LuCy4n3/SmartPotProject/Programmer/iot-sunxi-driver/Documentation/images/DotNetIotRoadmapComponents.png

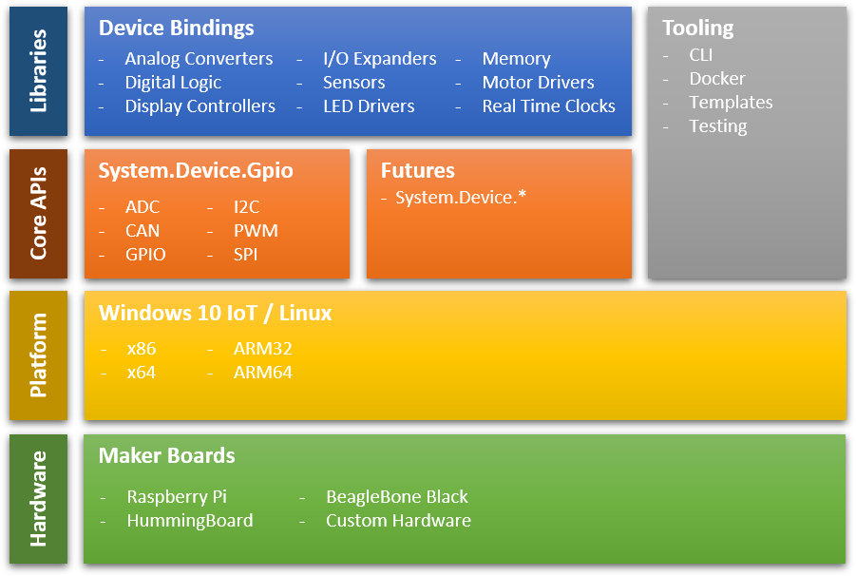
Programmer/iot-sunxi-driver/Documentation/images/DotNetIotRoadmapComponents.png
