LuCy4n3/SmartPotProject/Programmer/Bottom - lumina normala.png

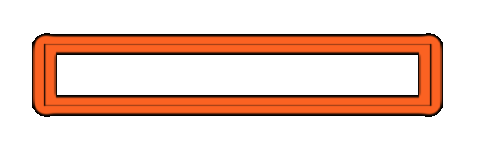
Programmer/Bottom - lumina normala.png
