LuCy4n3/SmartPotProject/Programmer/iot-sunxi-driver/Documentation/images/configurations.png

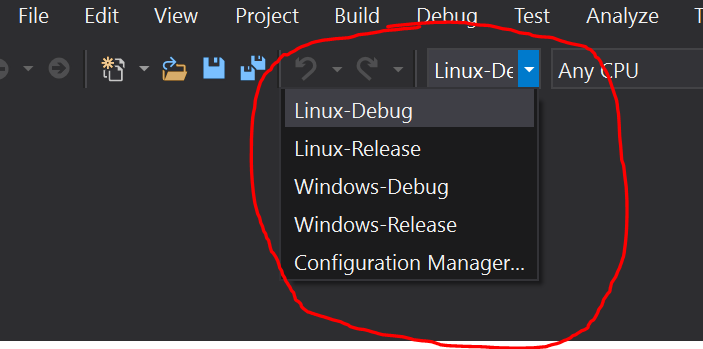
Programmer/iot-sunxi-driver/Documentation/images/configurations.png
