LuCy4n3/SmartPotProject/Programmer/iot-sunxi-driver/samples/force-sensitive-resistor/Fsr408_Capacitor_RaspPi.png

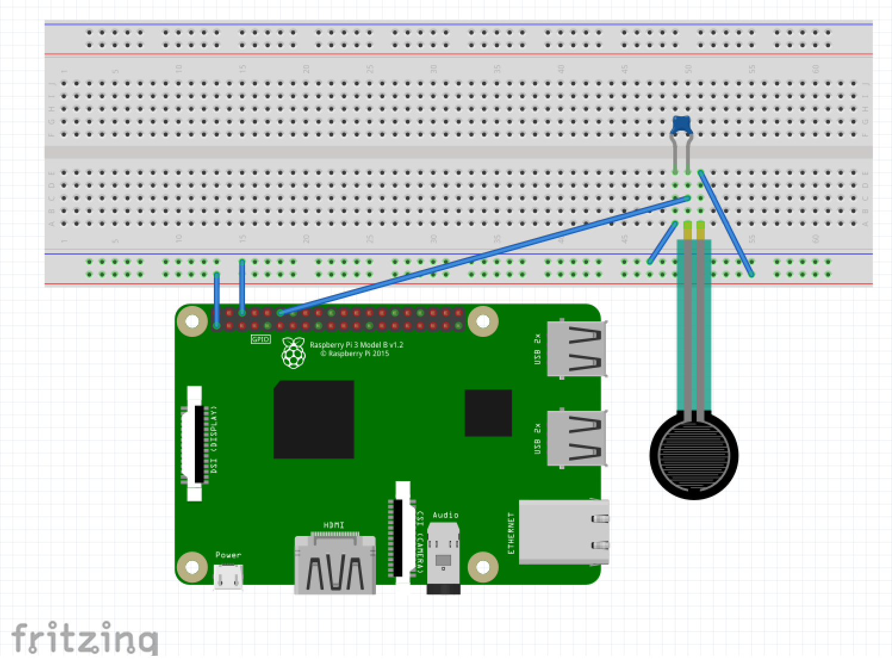
Programmer/iot-sunxi-driver/samples/force-sensitive-resistor/Fsr408_Capacitor_RaspPi.png
