LuCy4n3/SmartPotProject/Programmer/iot-sunxi-driver/samples/force-sensitive-resistor/Fsr408_Mcp3008_RaspPi.png

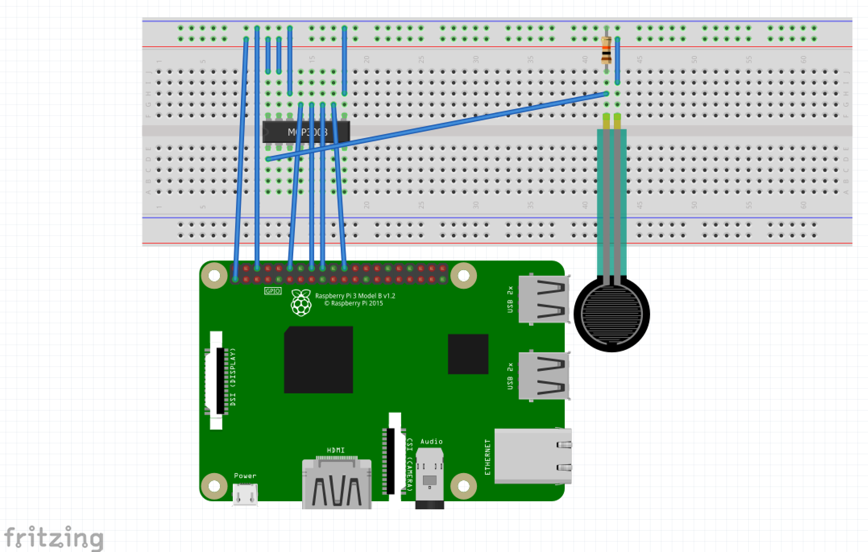
Programmer/iot-sunxi-driver/samples/force-sensitive-resistor/Fsr408_Mcp3008_RaspPi.png
