LuCy4n3/SmartPotProject/Programmer/iot-sunxi-driver/samples/led-blink/rpi-led_bb.png

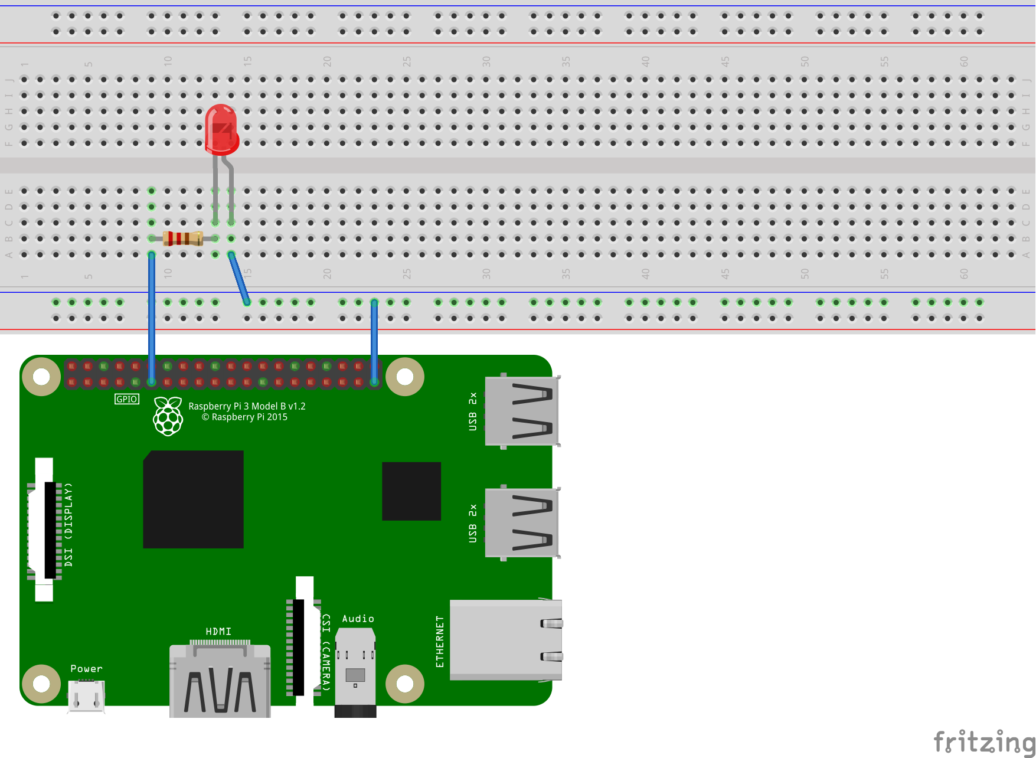
Programmer/iot-sunxi-driver/samples/led-blink/rpi-led_bb.png
