LuCy4n3/SmartPotProject/Programmer/iot-sunxi-driver/samples/led-matrix-weather/chaining-matrices.jpg

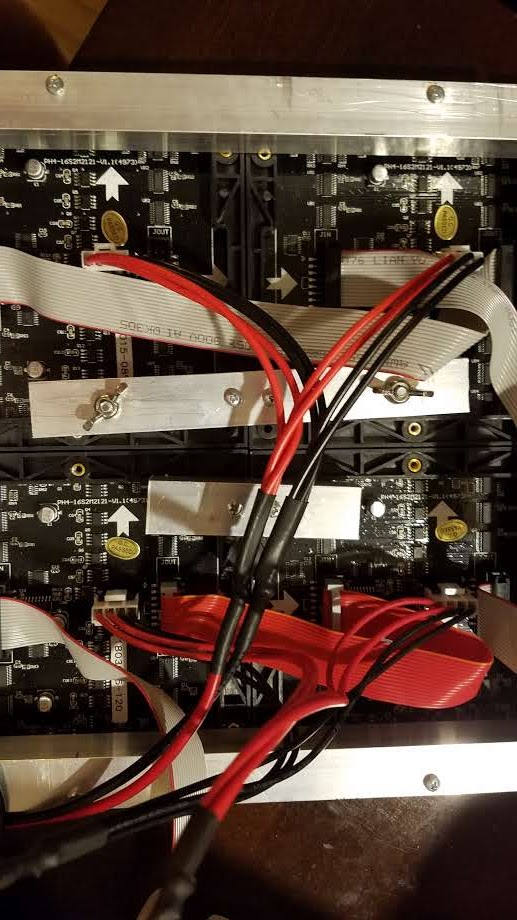
Programmer/iot-sunxi-driver/samples/led-matrix-weather/chaining-matrices.jpg
