LuCy4n3/SmartPotProject/Programmer/iot-sunxi-driver/samples/led-matrix-weather/pi-with-bonnet.jpg

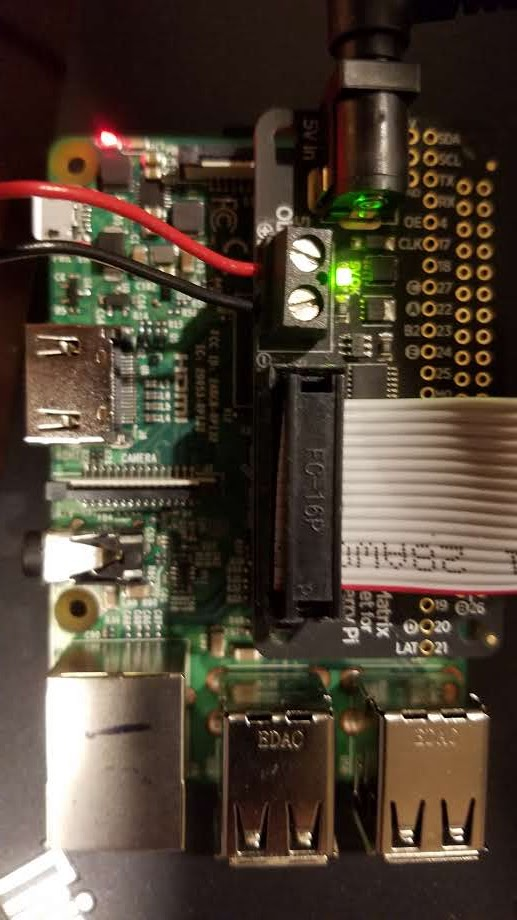
Programmer/iot-sunxi-driver/samples/led-matrix-weather/pi-with-bonnet.jpg
