LuCy4n3/SmartPotProject/Programmer/iot-sunxi-driver/samples/led-matrix-weather/rain.jpg

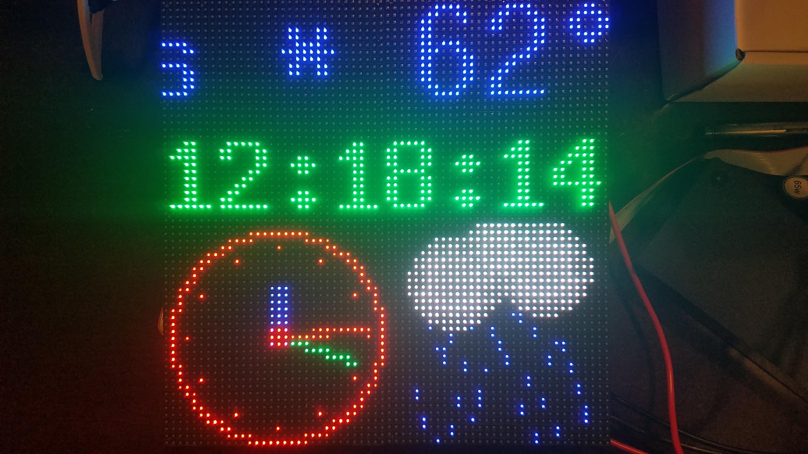
Programmer/iot-sunxi-driver/samples/led-matrix-weather/rain.jpg
