LuCy4n3/SmartPotProject/Programmer/iot-sunxi-driver/samples/led-more-blinking-lights/rpi-more-blinking-lights_bb.png

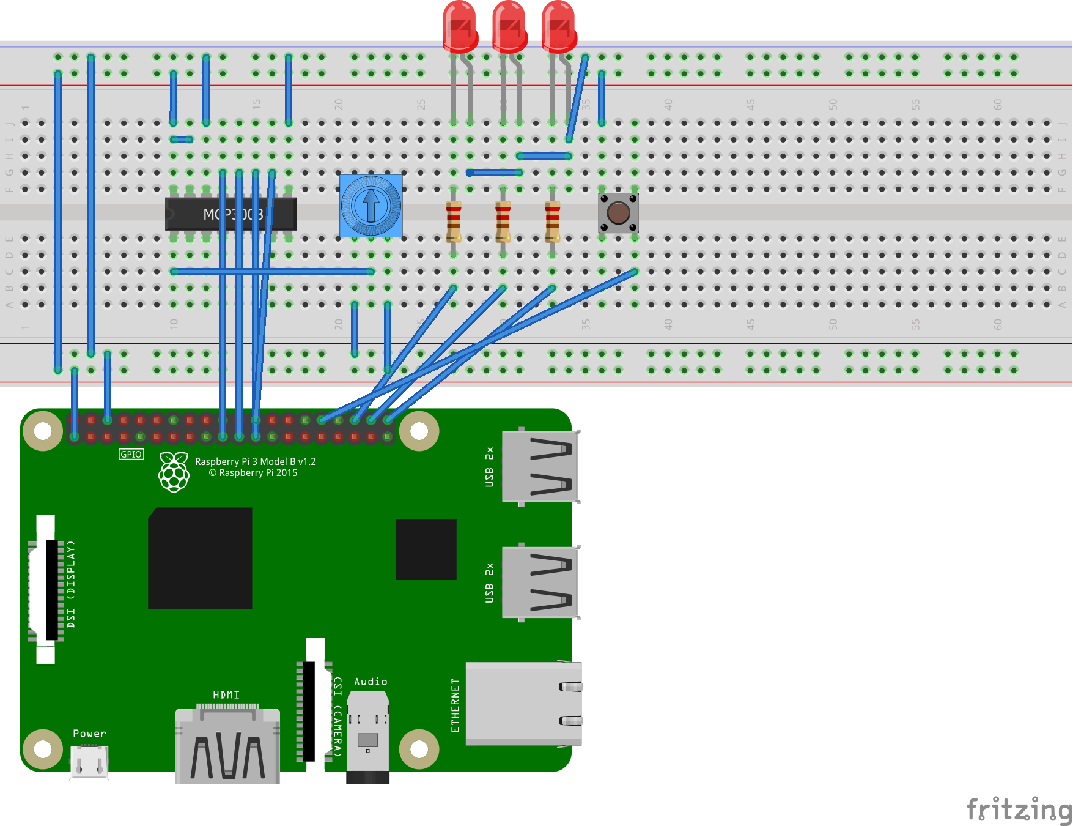
Programmer/iot-sunxi-driver/samples/led-more-blinking-lights/rpi-more-blinking-lights_bb.png
