LuCy4n3/SmartPotProject/Programmer/iot-sunxi-driver/samples/serialport-arduino/arduino-pi-sp_bb.png

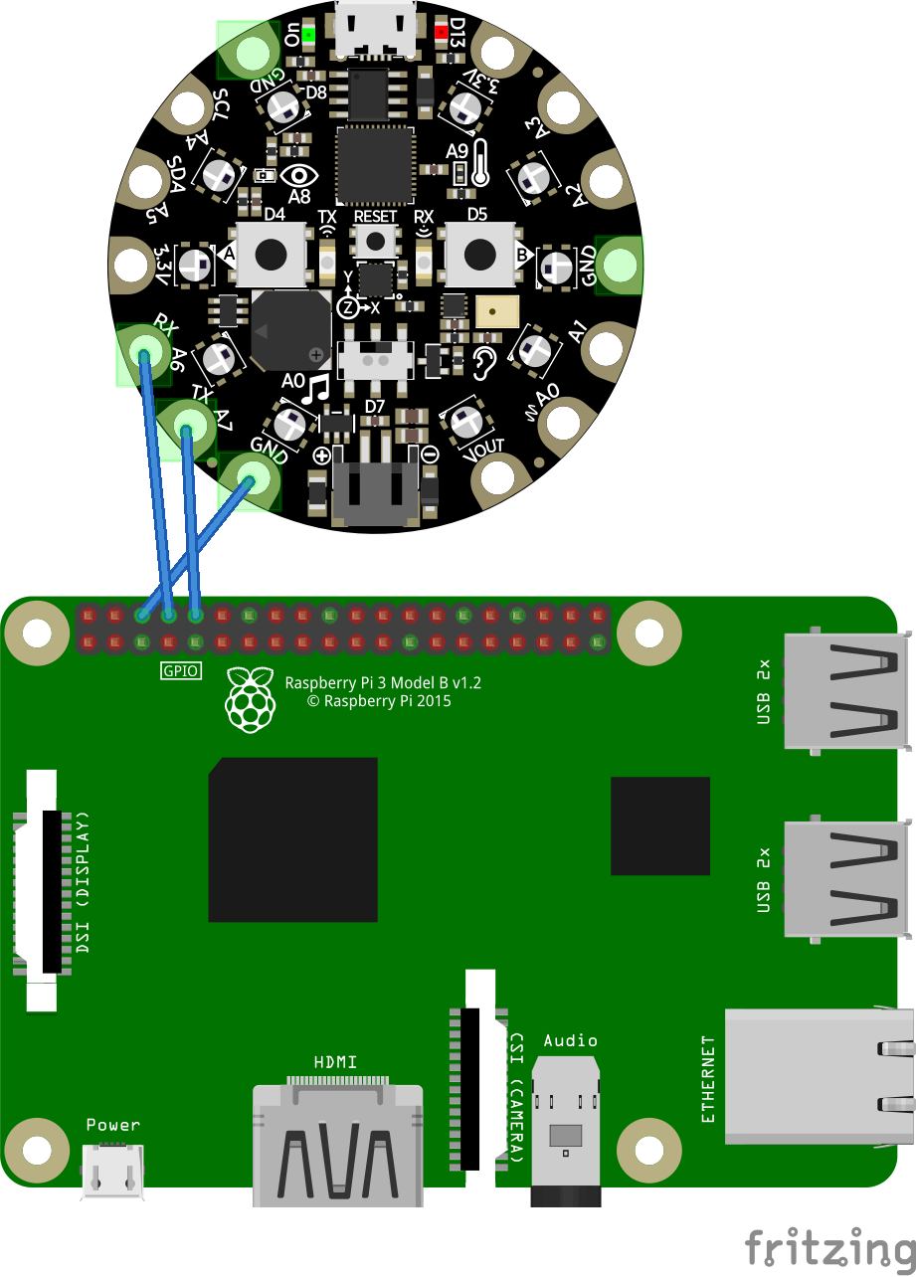
Programmer/iot-sunxi-driver/samples/serialport-arduino/arduino-pi-sp_bb.png
