LuCy4n3/SmartPotProject/Programmer/iot-sunxi-driver/src/devices/Ads1115/samples/ADS1115_circuit_bb.png

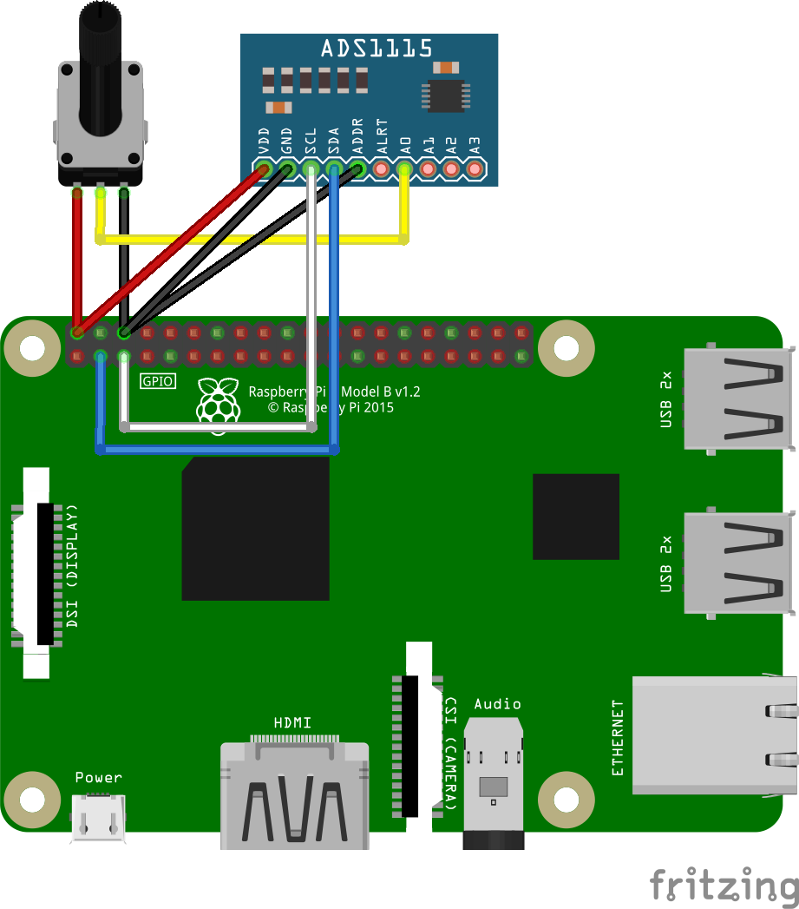
Programmer/iot-sunxi-driver/src/devices/Ads1115/samples/ADS1115_circuit_bb.png
