LuCy4n3/SmartPotProject/Programmer/iot-sunxi-driver/src/devices/Ads1115/sensor.jpg

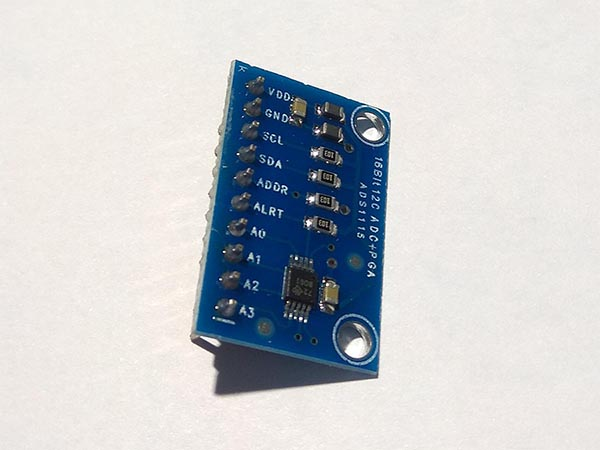
Programmer/iot-sunxi-driver/src/devices/Ads1115/sensor.jpg
