LuCy4n3/SmartPotProject/Programmer/iot-sunxi-driver/src/devices/Adxl345/samples/ADXL345_circuit_bb.png

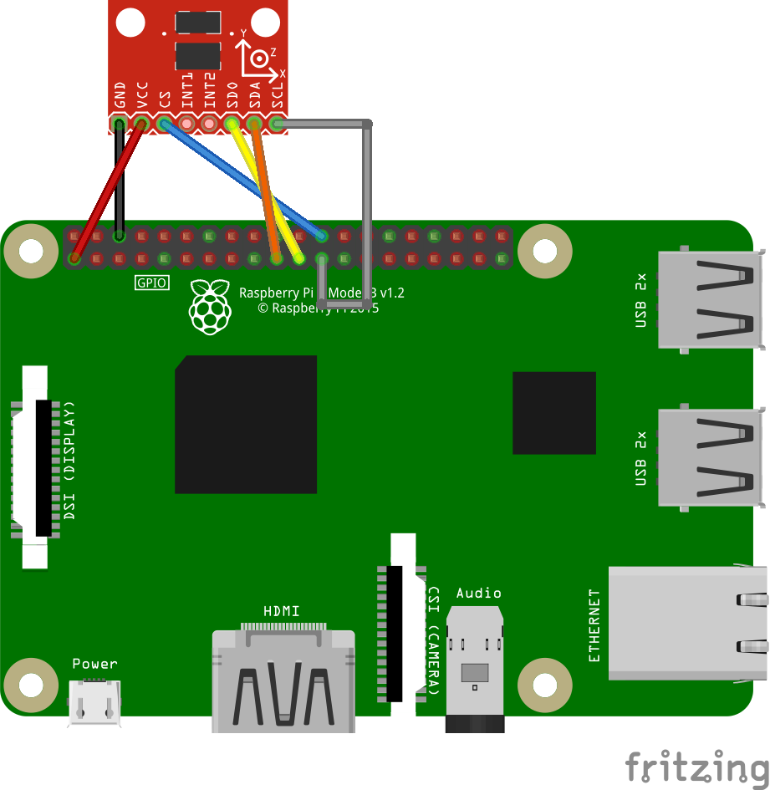
Programmer/iot-sunxi-driver/src/devices/Adxl345/samples/ADXL345_circuit_bb.png
