LuCy4n3/SmartPotProject/Programmer/iot-sunxi-driver/src/devices/Adxl345/sensor.jpg

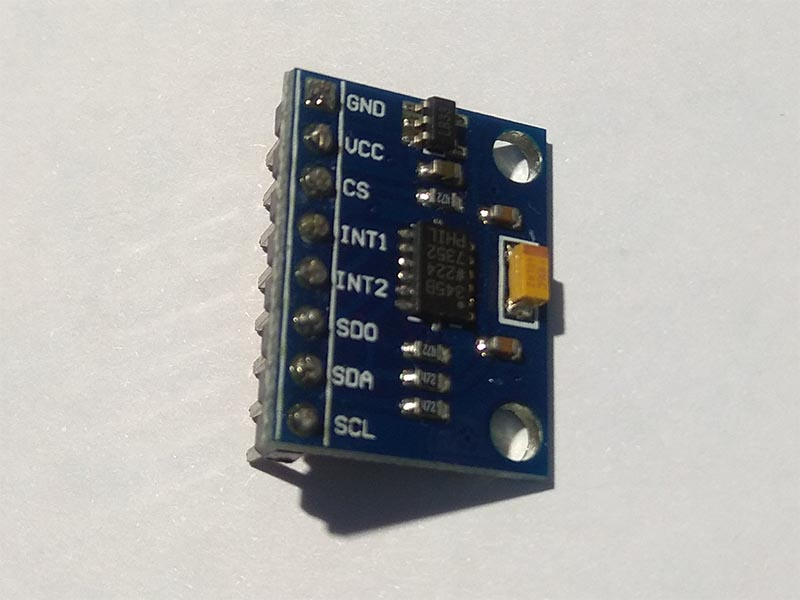
Programmer/iot-sunxi-driver/src/devices/Adxl345/sensor.jpg
