LuCy4n3/SmartPotProject/Programmer/iot-sunxi-driver/src/devices/Ags01db/samples/AGS01DB_circuit_bb.png

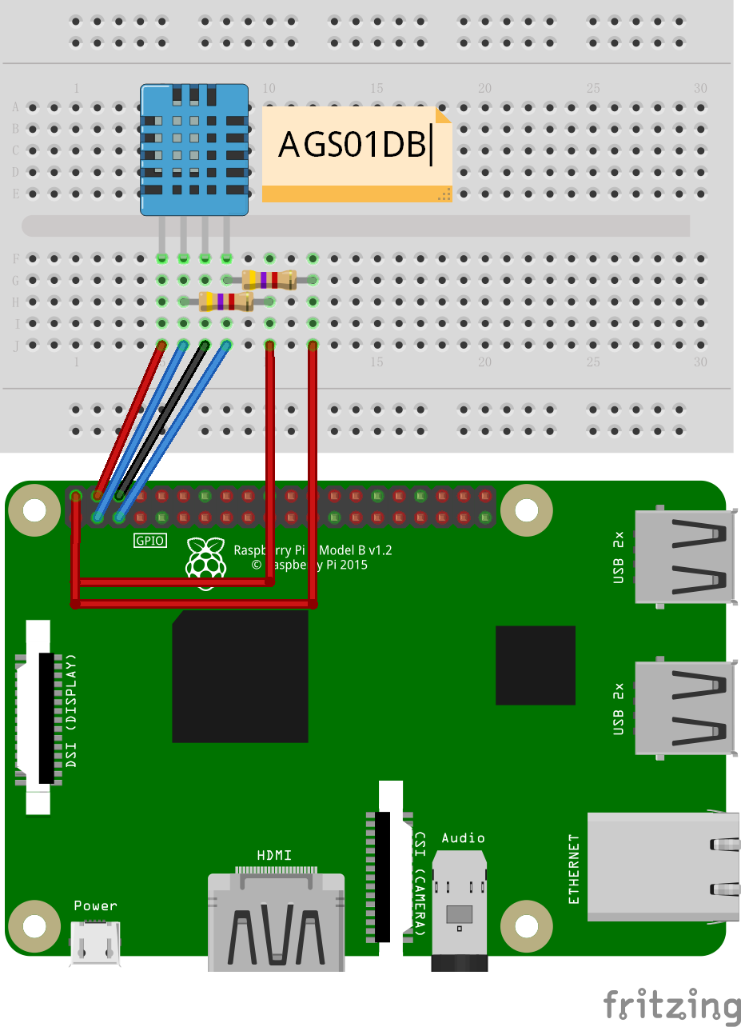
Programmer/iot-sunxi-driver/src/devices/Ags01db/samples/AGS01DB_circuit_bb.png
