LuCy4n3/SmartPotProject/Programmer/iot-sunxi-driver/src/devices/Ags01db/sensor.jpg

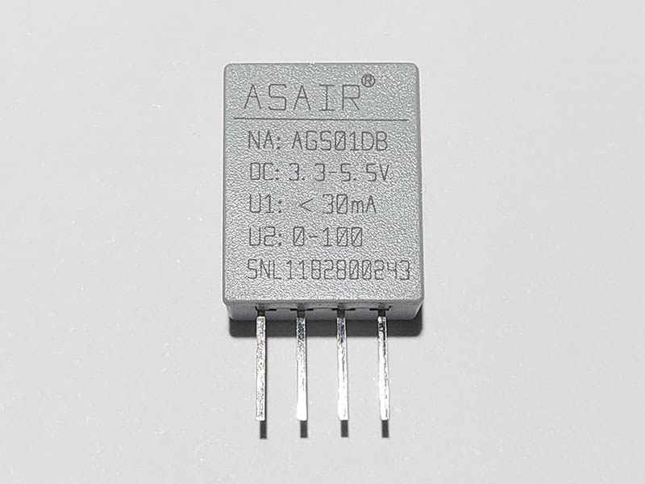
Programmer/iot-sunxi-driver/src/devices/Ags01db/sensor.jpg
