LuCy4n3/SmartPotProject/Programmer/iot-sunxi-driver/src/devices/Ak8963/corrcalib.png

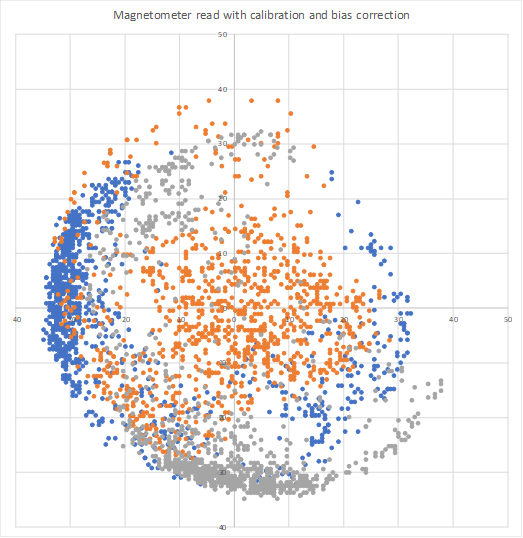
Programmer/iot-sunxi-driver/src/devices/Ak8963/corrcalib.png
