LuCy4n3/SmartPotProject/Programmer/iot-sunxi-driver/src/devices/Ak8963/rawcalib.png

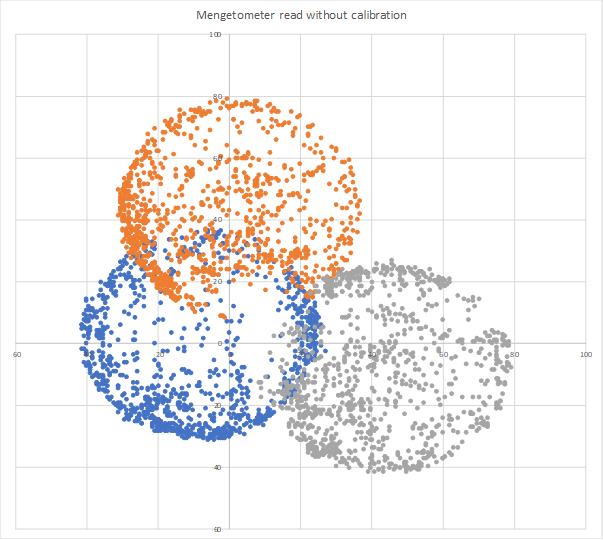
Programmer/iot-sunxi-driver/src/devices/Ak8963/rawcalib.png
