LuCy4n3/SmartPotProject/Programmer/iot-sunxi-driver/src/devices/Bh1745/sensor.jpg

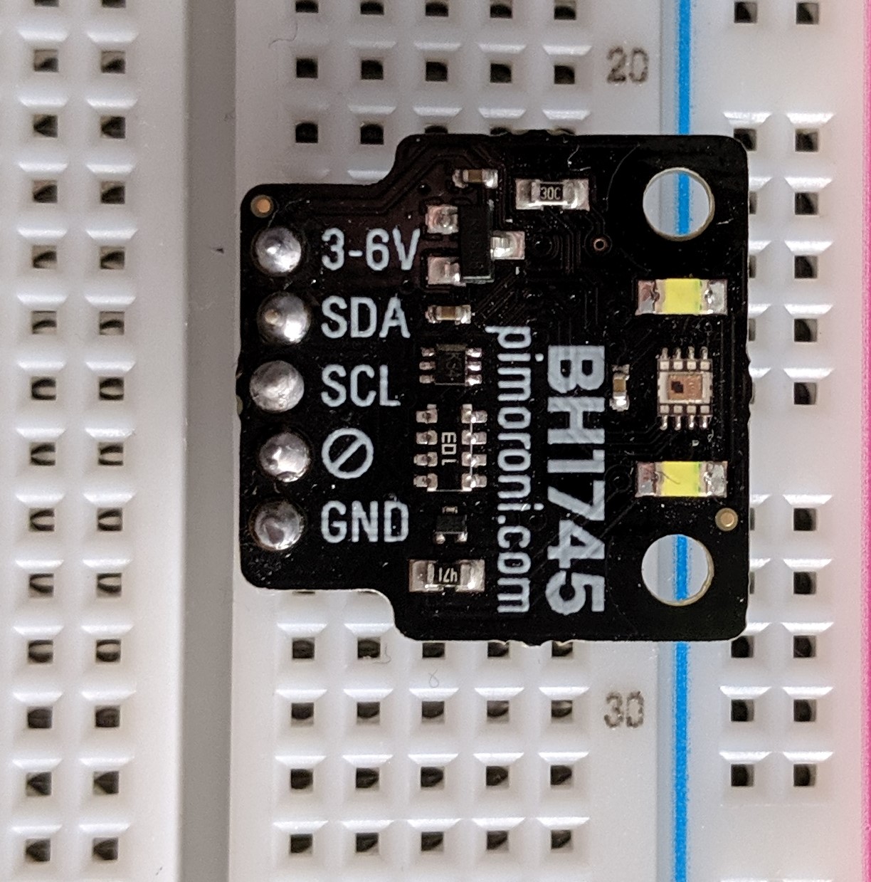
Programmer/iot-sunxi-driver/src/devices/Bh1745/sensor.jpg
