LuCy4n3/SmartPotProject/Programmer/iot-sunxi-driver/src/devices/Bh1750fvi/samples/BH1750FVI_Circuit_bb.png

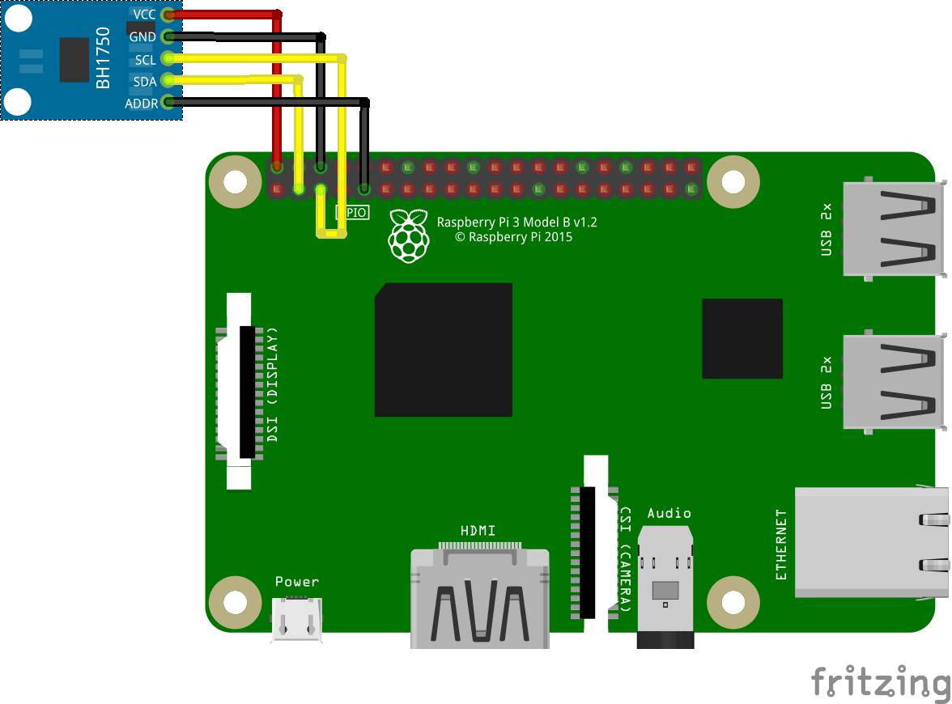
Programmer/iot-sunxi-driver/src/devices/Bh1750fvi/samples/BH1750FVI_Circuit_bb.png
