LuCy4n3/SmartPotProject/Programmer/iot-sunxi-driver/src/devices/Bh1750fvi/sensor.jpg

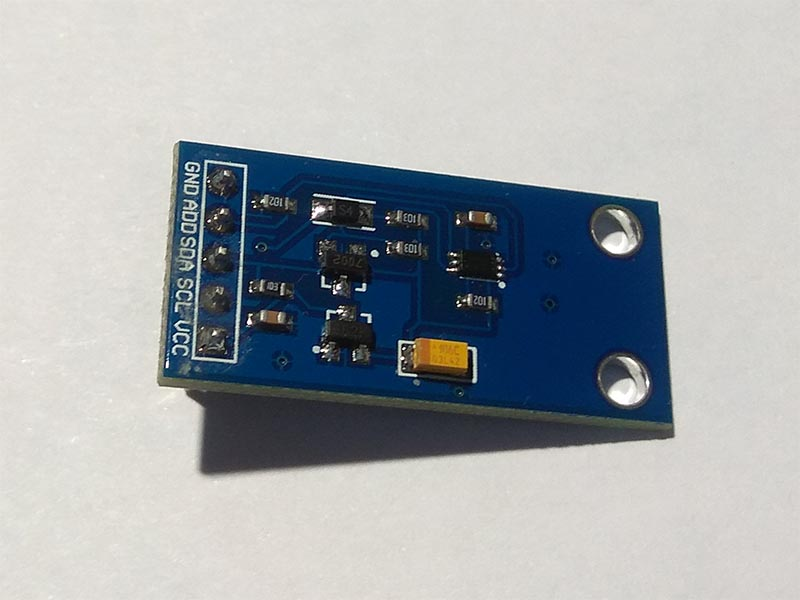
Programmer/iot-sunxi-driver/src/devices/Bh1750fvi/sensor.jpg
