LuCy4n3/SmartPotProject/Programmer/iot-sunxi-driver/src/devices/Bmp180/samples/rpi-bmp180_i2c_bb.png

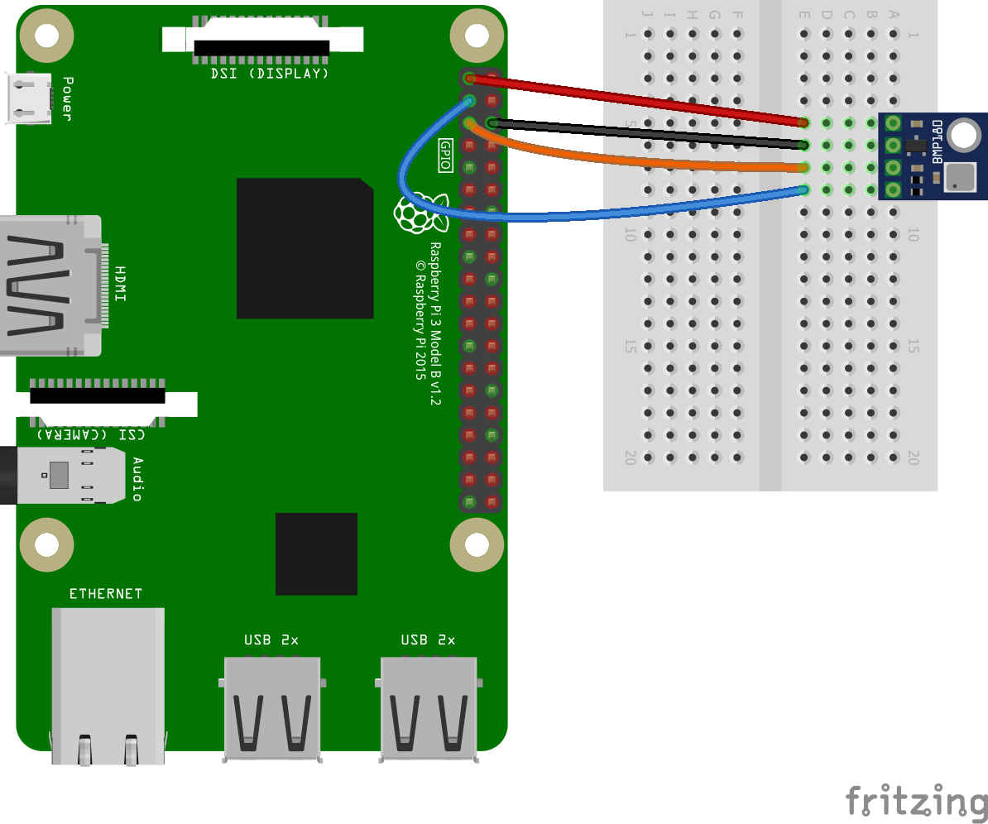
Programmer/iot-sunxi-driver/src/devices/Bmp180/samples/rpi-bmp180_i2c_bb.png
