LuCy4n3/SmartPotProject/Programmer/iot-sunxi-driver/src/devices/Bmxx80/samples/rpi-bmp280_i2c.png

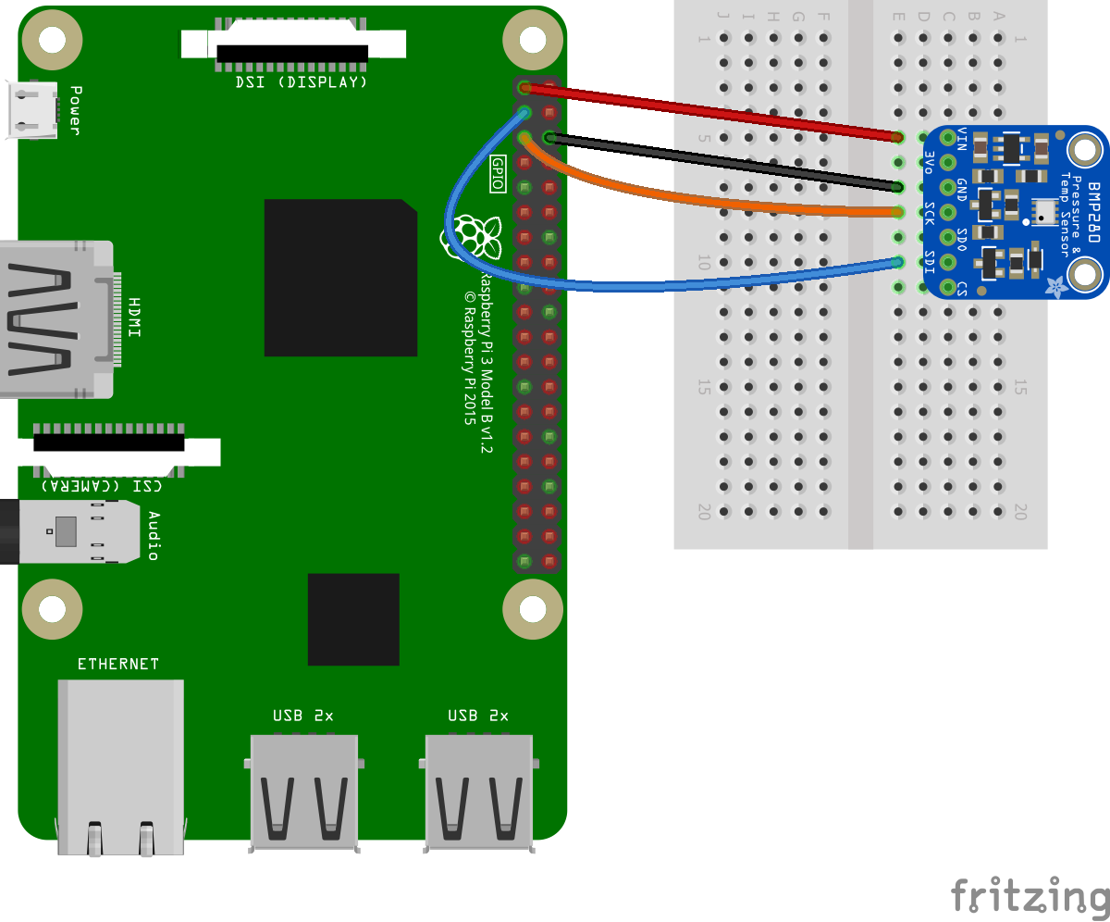
Programmer/iot-sunxi-driver/src/devices/Bmxx80/samples/rpi-bmp280_i2c.png
