LuCy4n3/SmartPotProject/Programmer/iot-sunxi-driver/src/devices/Bno055/BNO055.jpg

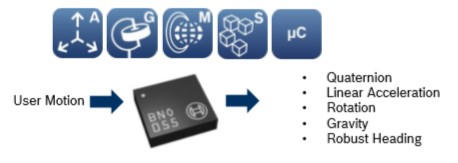
Programmer/iot-sunxi-driver/src/devices/Bno055/BNO055.jpg
