LuCy4n3/SmartPotProject/Programmer/iot-sunxi-driver/src/devices/BrickPi3/BrickPi3-How-it-Works.jpg

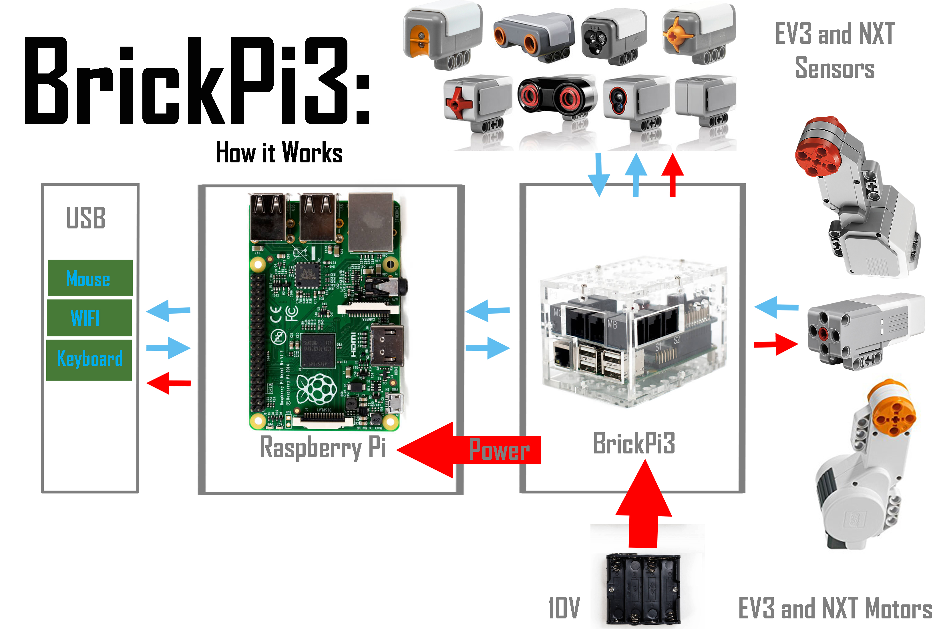
Programmer/iot-sunxi-driver/src/devices/BrickPi3/BrickPi3-How-it-Works.jpg
