LuCy4n3/SmartPotProject/Programmer/iot-sunxi-driver/src/devices/DCMotor/samples/dcmotor_bb.png

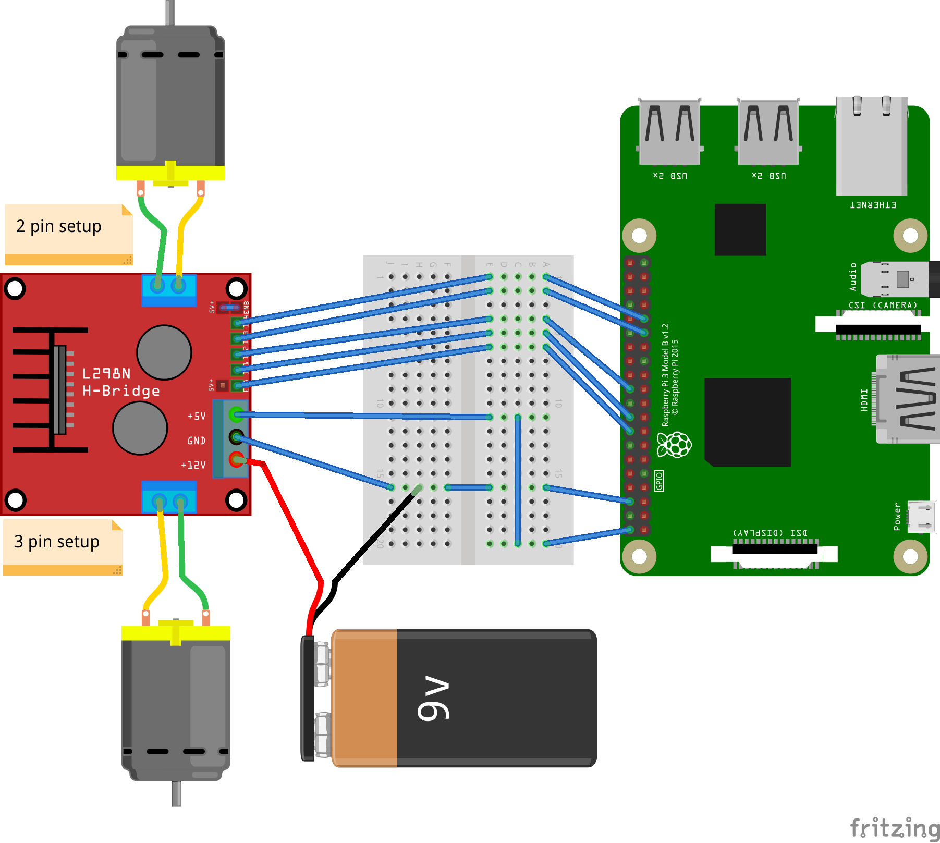
Programmer/iot-sunxi-driver/src/devices/DCMotor/samples/dcmotor_bb.png
