LuCy4n3/SmartPotProject/Programmer/iot-sunxi-driver/src/devices/Dhtxx/imgs/dht11.jpg

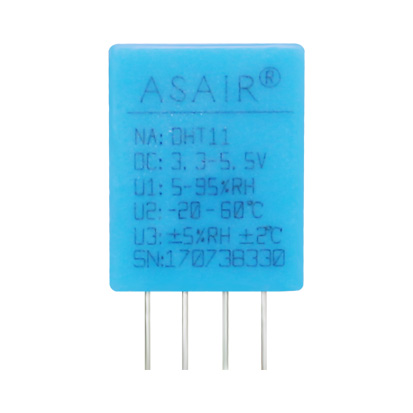
Programmer/iot-sunxi-driver/src/devices/Dhtxx/imgs/dht11.jpg
