LuCy4n3/SmartPotProject/Programmer/iot-sunxi-driver/src/devices/Dhtxx/samples/dht22.png

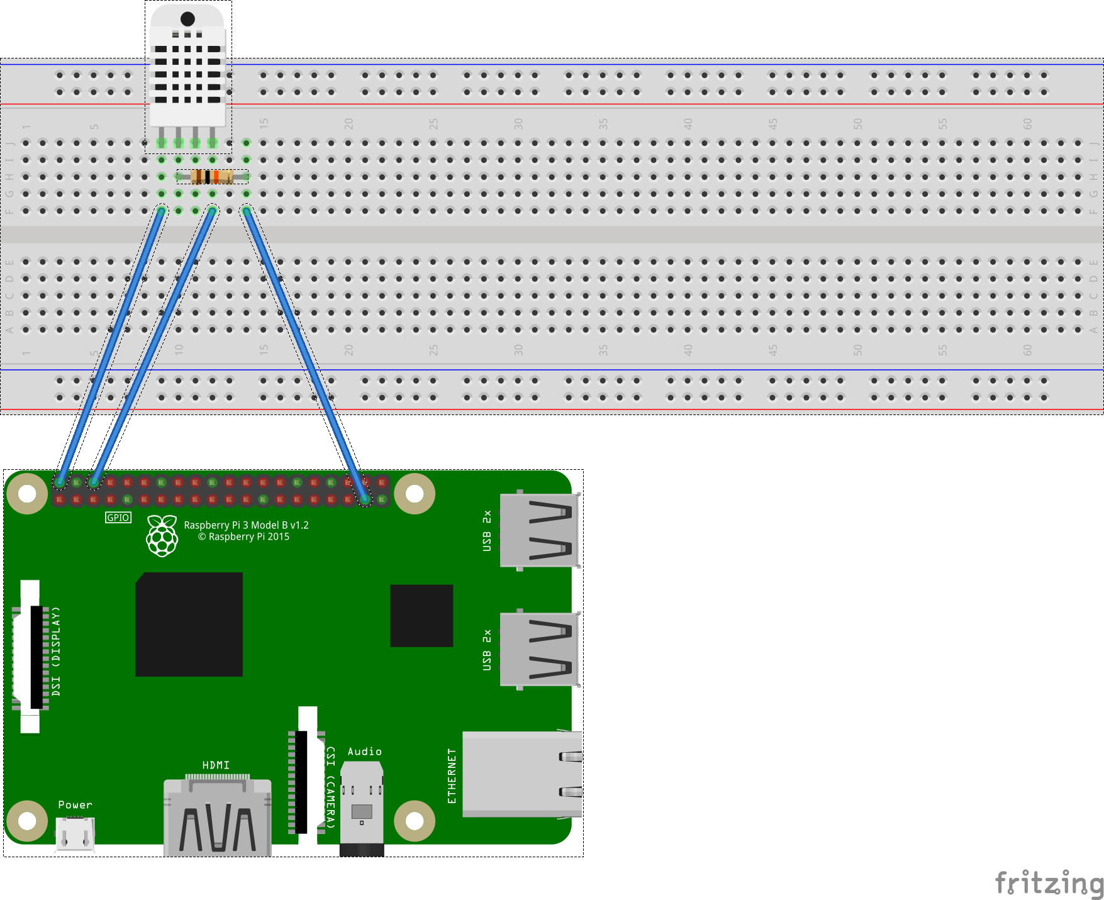
Programmer/iot-sunxi-driver/src/devices/Dhtxx/samples/dht22.png
