LuCy4n3/SmartPotProject/Programmer/iot-sunxi-driver/src/devices/Dhtxx/samples/dht22ex.jpg

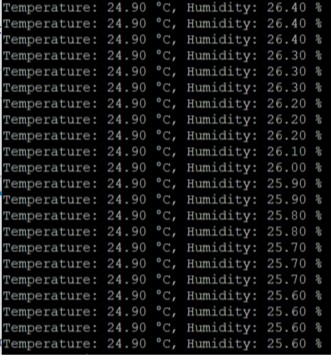
Programmer/iot-sunxi-driver/src/devices/Dhtxx/samples/dht22ex.jpg
