LuCy4n3/SmartPotProject/Programmer/iot-sunxi-driver/src/devices/GoPiGo3/GoPiGo3.png

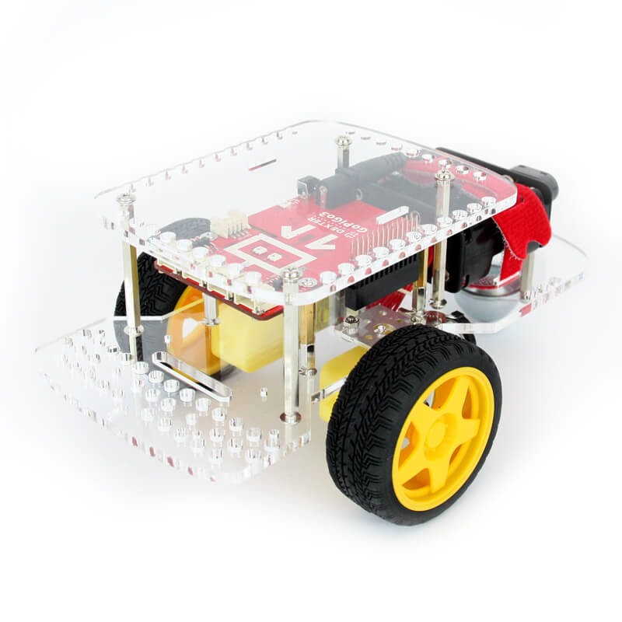
Programmer/iot-sunxi-driver/src/devices/GoPiGo3/GoPiGo3.png
