LuCy4n3/SmartPotProject/Programmer/iot-sunxi-driver/src/devices/GoPiGo3/gopigosensors.png

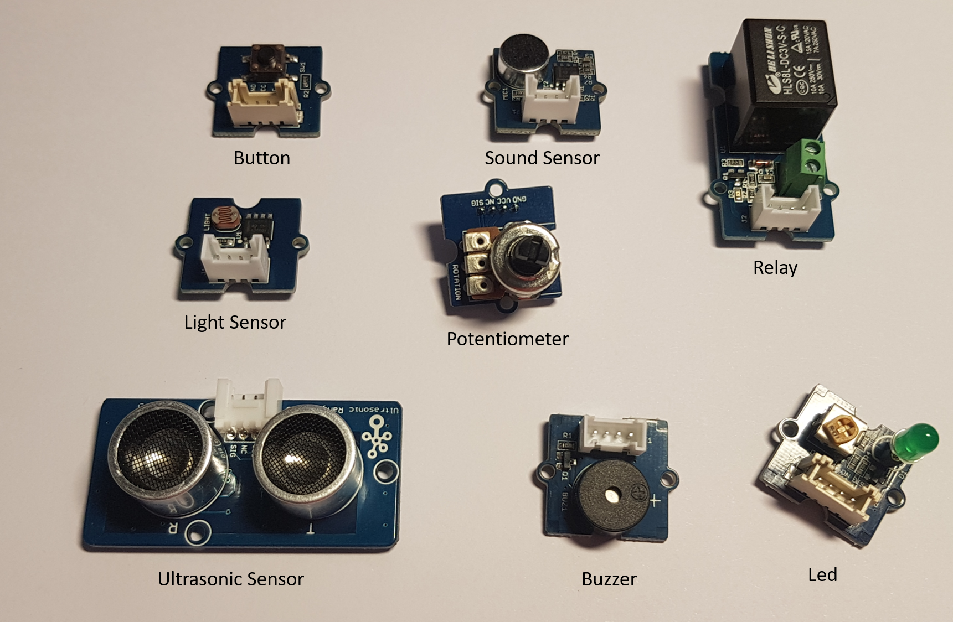
Programmer/iot-sunxi-driver/src/devices/GoPiGo3/gopigosensors.png
