LuCy4n3/SmartPotProject/Programmer/iot-sunxi-driver/src/devices/GrovePi/grovepi.jpg

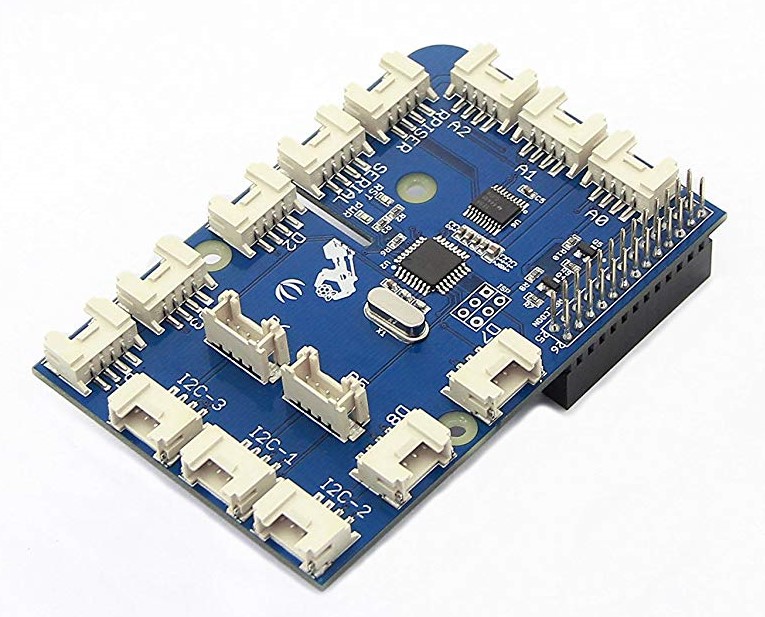
Programmer/iot-sunxi-driver/src/devices/GrovePi/grovepi.jpg
