LuCy4n3/SmartPotProject/Programmer/iot-sunxi-driver/src/devices/GrovePi/GrovePort.png

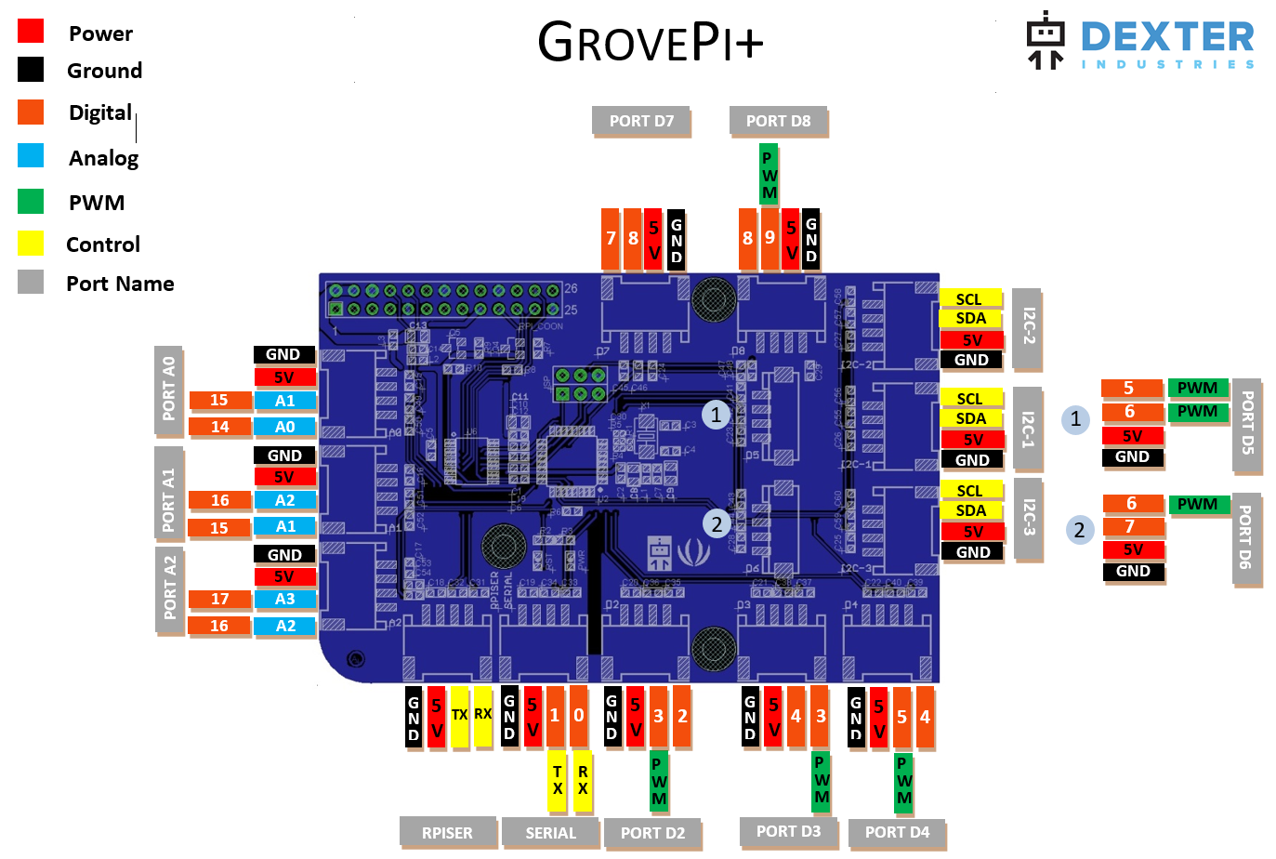
Programmer/iot-sunxi-driver/src/devices/GrovePi/GrovePort.png
