LuCy4n3/SmartPotProject/Programmer/iot-sunxi-driver/src/devices/GrovePi/samples/sample.jpg

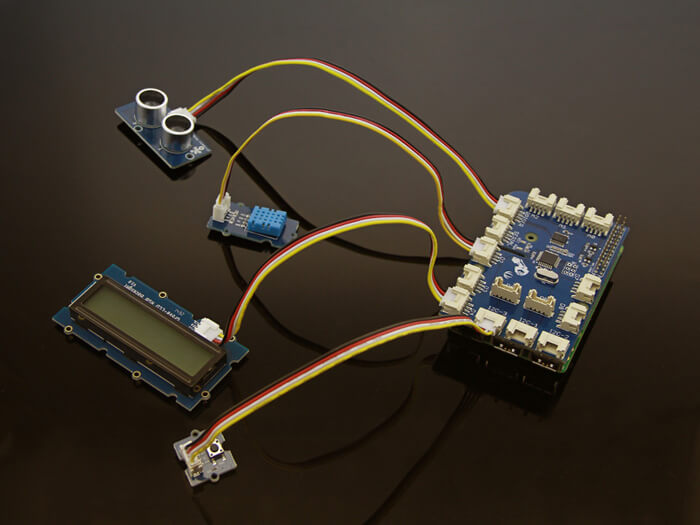
Programmer/iot-sunxi-driver/src/devices/GrovePi/samples/sample.jpg
