LuCy4n3/SmartPotProject/Programmer/iot-sunxi-driver/src/devices/Hcsr04/samples/raspberry_hc-sr04.png

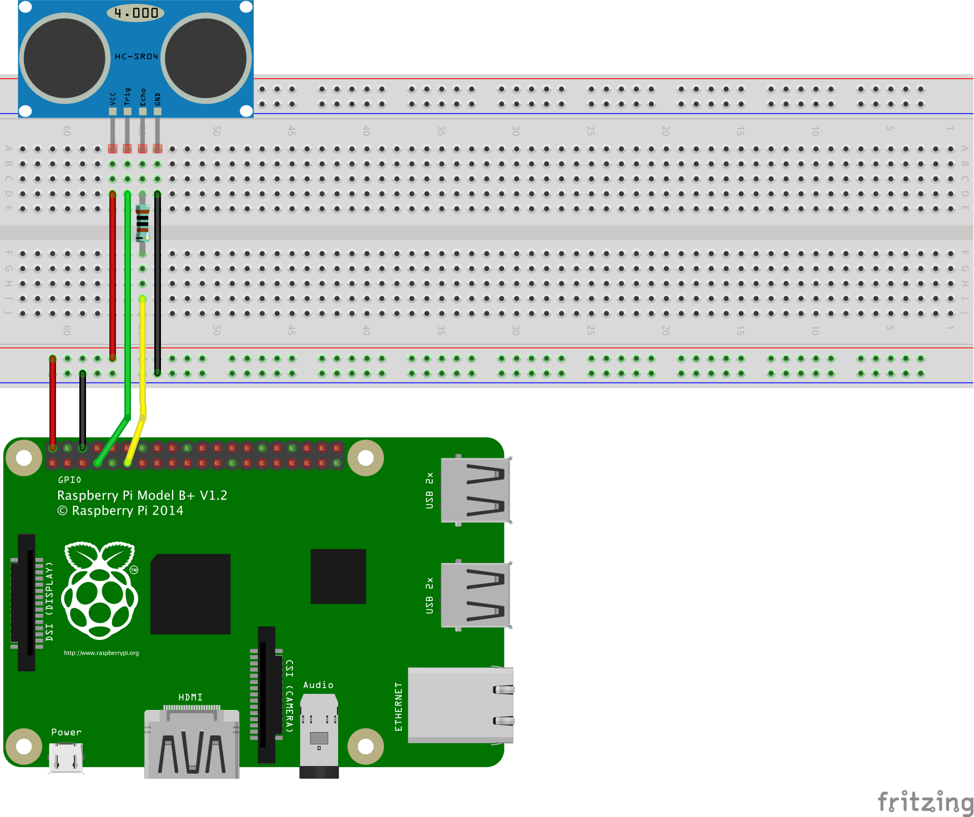
Programmer/iot-sunxi-driver/src/devices/Hcsr04/samples/raspberry_hc-sr04.png
