LuCy4n3/SmartPotProject/Programmer/iot-sunxi-driver/src/devices/Hcsr501/samples/circuit_bb.png

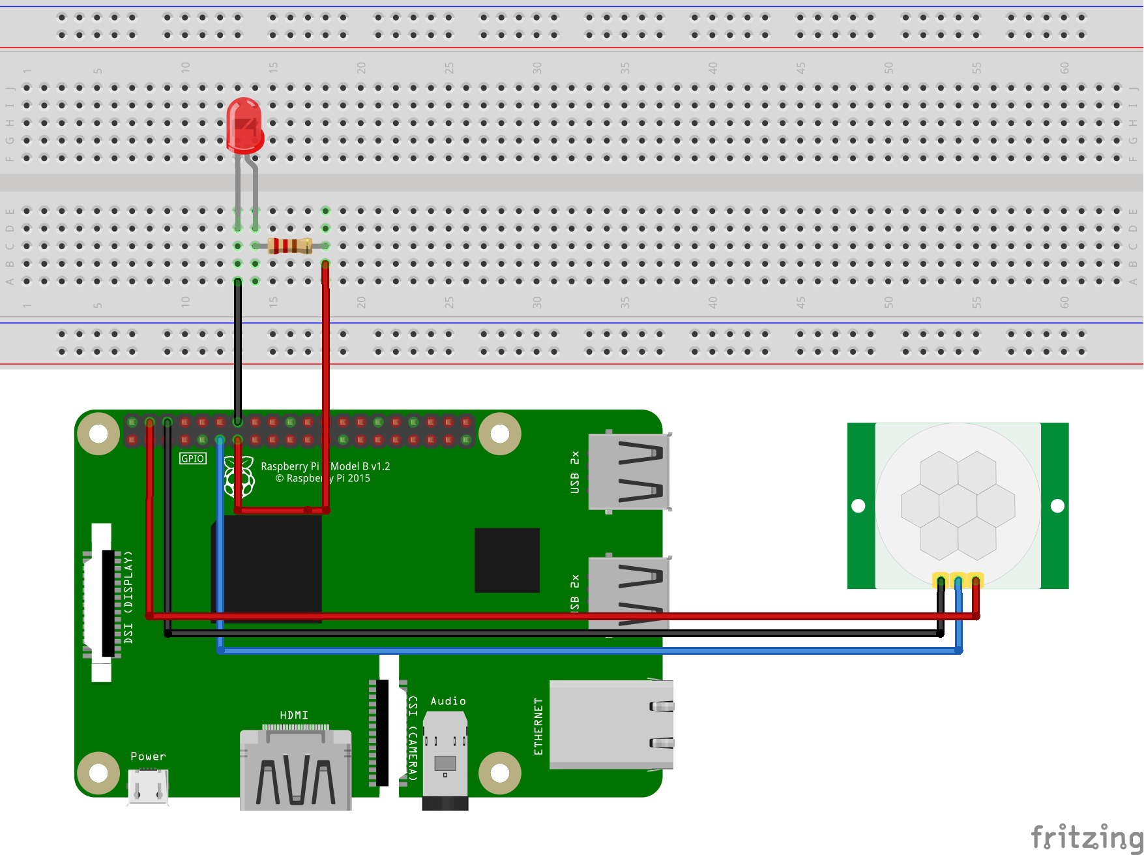
Programmer/iot-sunxi-driver/src/devices/Hcsr501/samples/circuit_bb.png
