LuCy4n3/SmartPotProject/Programmer/iot-sunxi-driver/src/devices/Hcsr501/samples/Hcsr501Setting.png

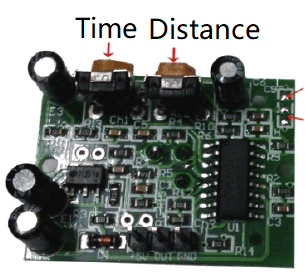
Programmer/iot-sunxi-driver/src/devices/Hcsr501/samples/Hcsr501Setting.png
