LuCy4n3/SmartPotProject/Programmer/iot-sunxi-driver/src/devices/Hcsr501/sensor.jpg

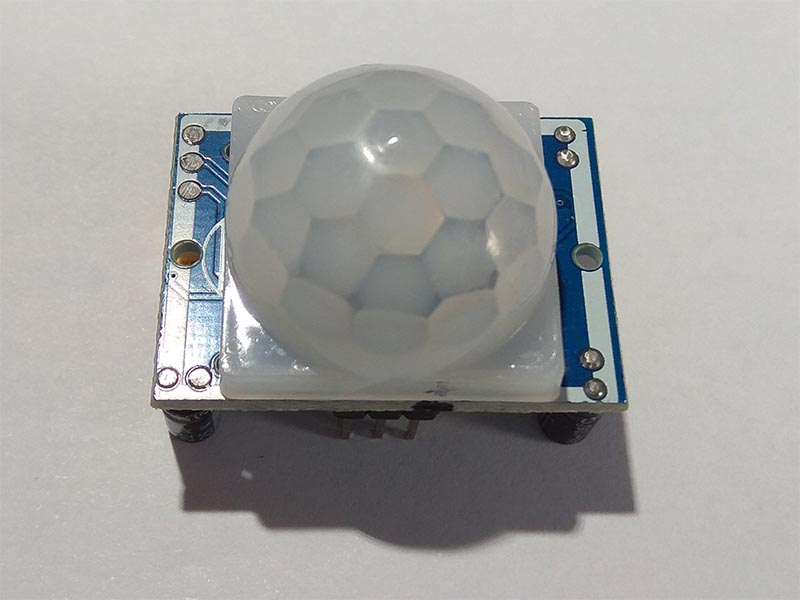
Programmer/iot-sunxi-driver/src/devices/Hcsr501/sensor.jpg
