LuCy4n3/SmartPotProject/Programmer/iot-sunxi-driver/src/devices/Hmc5883l/samples/HMC5883L_circuit_bb.png

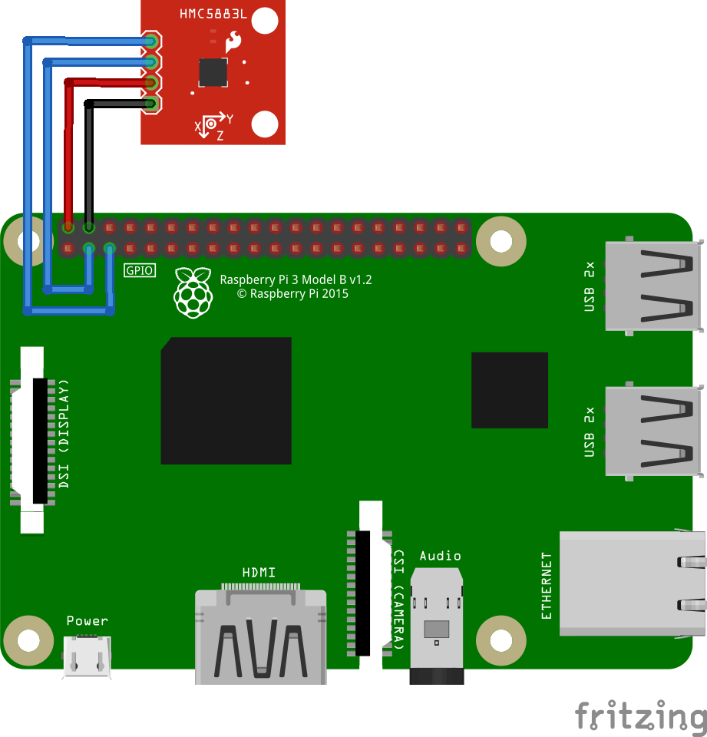
Programmer/iot-sunxi-driver/src/devices/Hmc5883l/samples/HMC5883L_circuit_bb.png
