LuCy4n3/SmartPotProject/Programmer/iot-sunxi-driver/src/devices/Hmc5883l/sensor.jpg

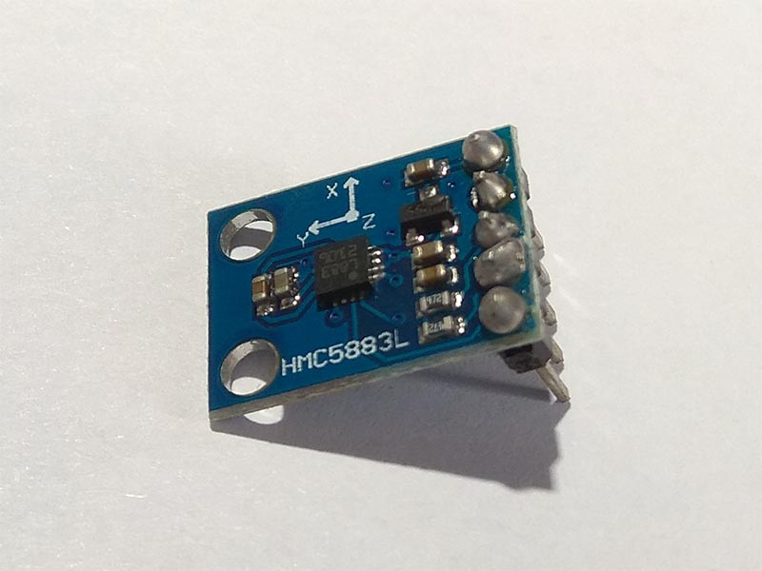
Programmer/iot-sunxi-driver/src/devices/Hmc5883l/sensor.jpg
