LuCy4n3/SmartPotProject/Programmer/iot-sunxi-driver/src/devices/Lm75/samples/LM75_circuit_bb.png

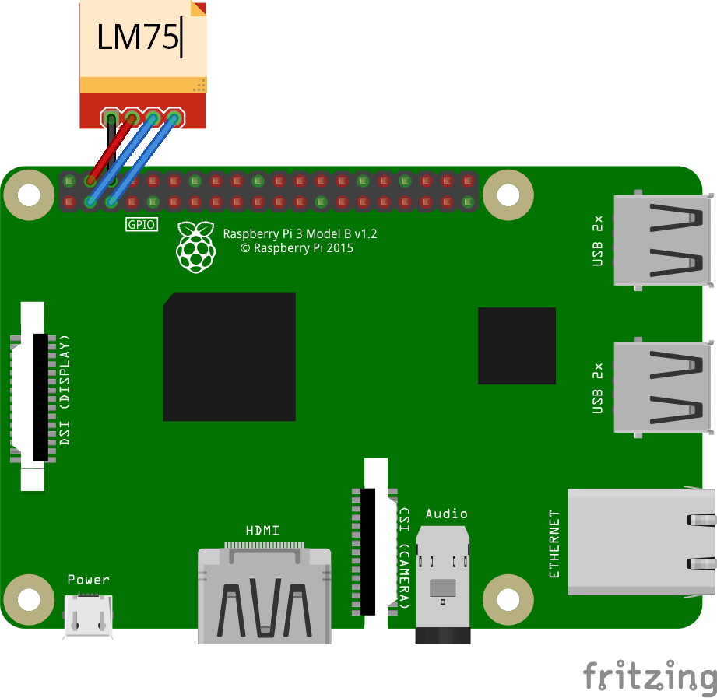
Programmer/iot-sunxi-driver/src/devices/Lm75/samples/LM75_circuit_bb.png
