LuCy4n3/SmartPotProject/Programmer/iot-sunxi-driver/src/devices/Max7219/samples/Schema_bb.png

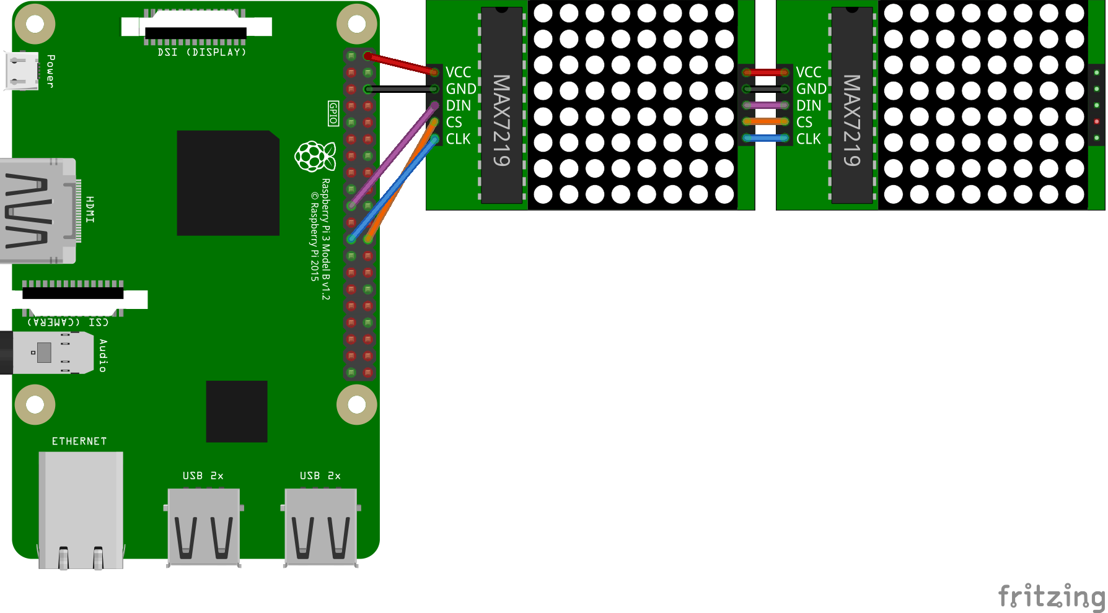
Programmer/iot-sunxi-driver/src/devices/Max7219/samples/Schema_bb.png
