LuCy4n3/SmartPotProject/Programmer/iot-sunxi-driver/src/devices/Max44009/sensor.jpg

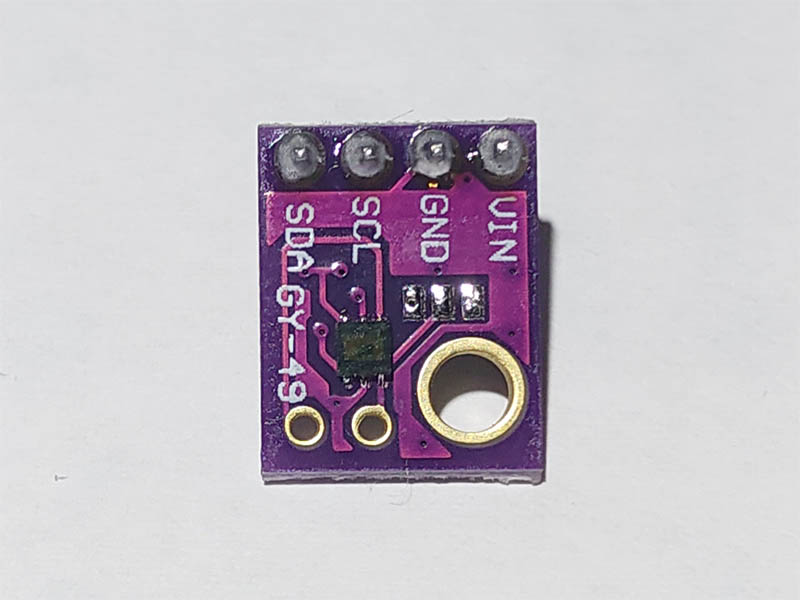
Programmer/iot-sunxi-driver/src/devices/Max44009/sensor.jpg
