LuCy4n3/SmartPotProject/Programmer/iot-sunxi-driver/src/devices/Mcp3xxx/samples/rpi-trimpot_gpio.png

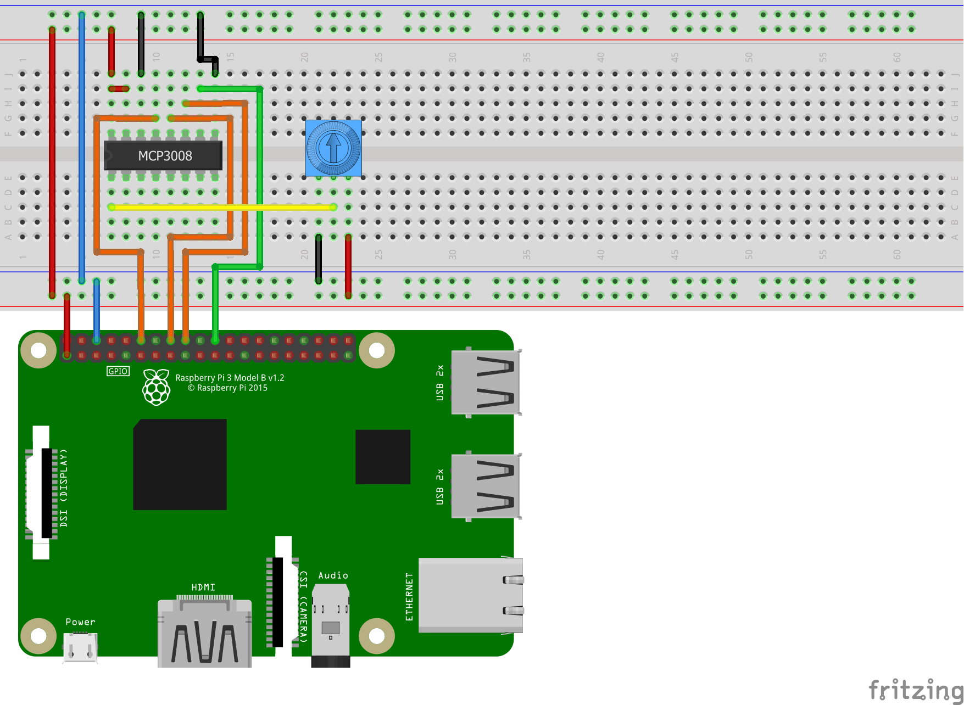
Programmer/iot-sunxi-driver/src/devices/Mcp3xxx/samples/rpi-trimpot_gpio.png
