LuCy4n3/SmartPotProject/Programmer/iot-sunxi-driver/src/devices/Mcp3xxx/samples/rpi-trimpot_spi.png

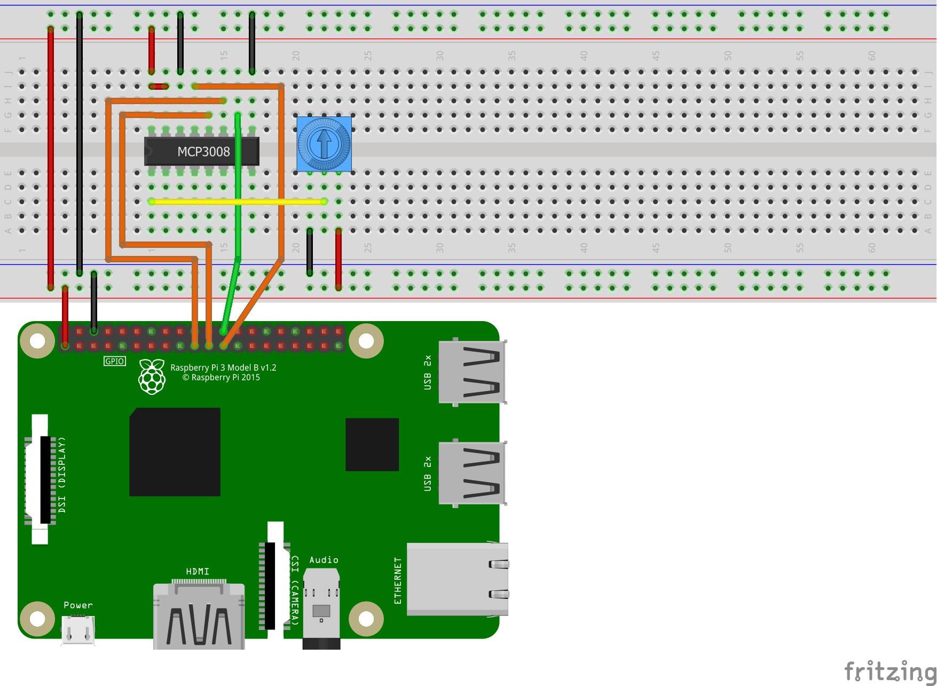
Programmer/iot-sunxi-driver/src/devices/Mcp3xxx/samples/rpi-trimpot_spi.png
