LuCy4n3/SmartPotProject/Programmer/iot-sunxi-driver/src/devices/Mcp23xxx/samples/Mcp23S17_I2c_ReadSwitches_WriteLeds.png

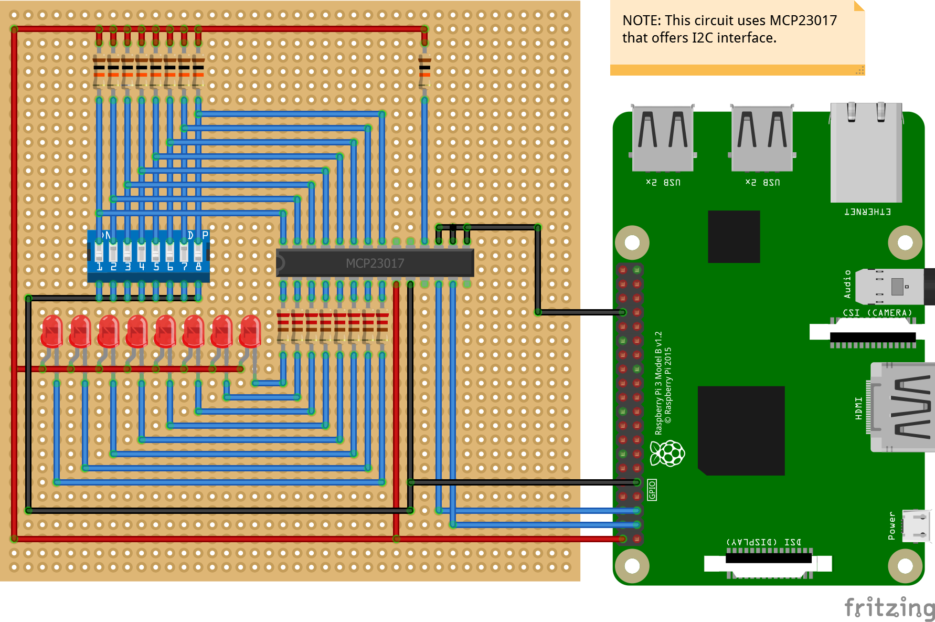
Programmer/iot-sunxi-driver/src/devices/Mcp23xxx/samples/Mcp23S17_I2c_ReadSwitches_WriteLeds.png
