LuCy4n3/SmartPotProject/Programmer/iot-sunxi-driver/src/devices/Mcp3428/samples/rpi_led_adc_i2c.png

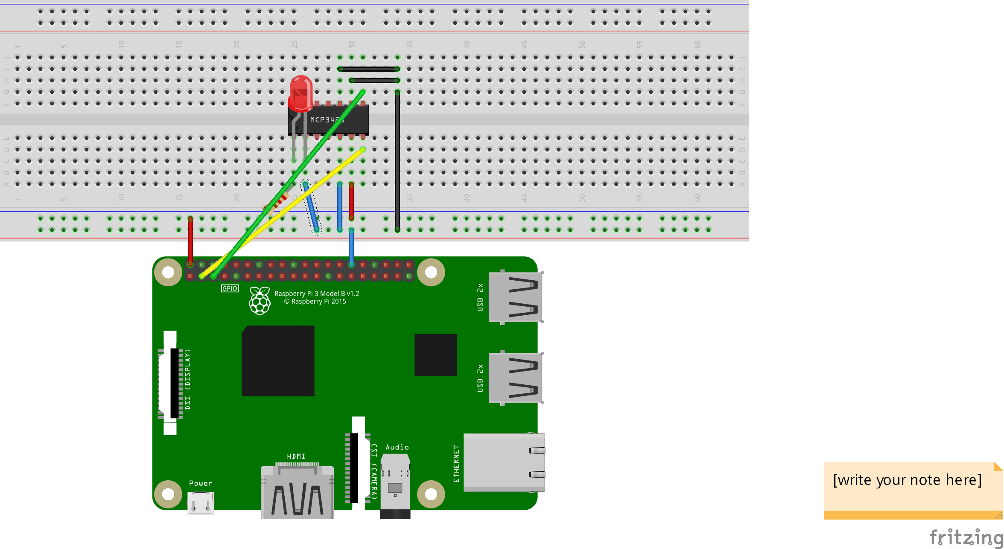
Programmer/iot-sunxi-driver/src/devices/Mcp3428/samples/rpi_led_adc_i2c.png
