LuCy4n3/SmartPotProject/Programmer/iot-sunxi-driver/src/devices/Mlx90614/samples/MLX90614_circuit_bb.jpg

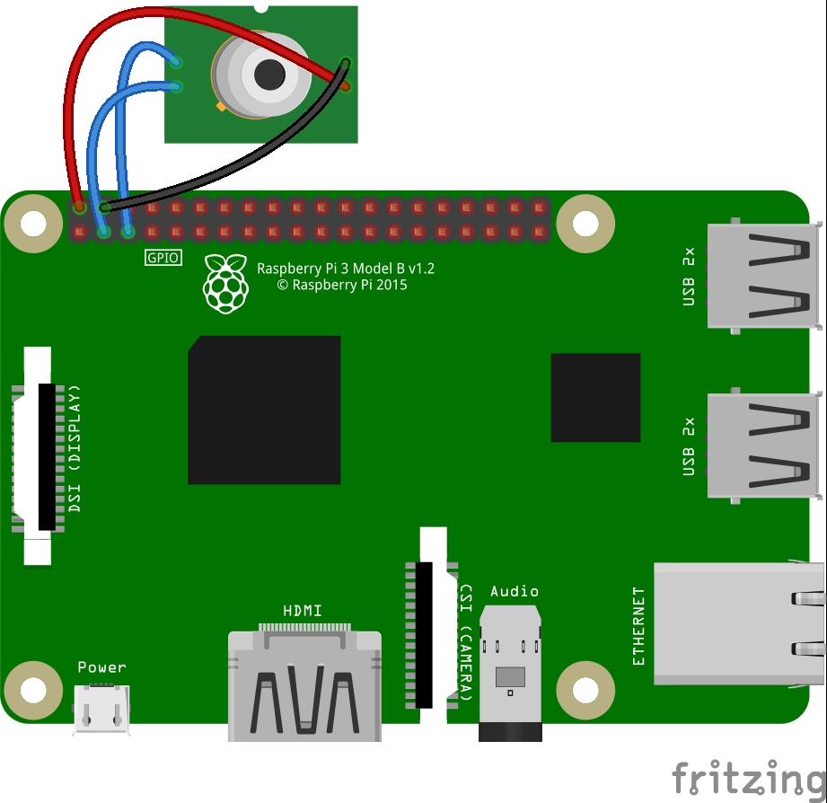
Programmer/iot-sunxi-driver/src/devices/Mlx90614/samples/MLX90614_circuit_bb.jpg
