LuCy4n3/SmartPotProject/Programmer/iot-sunxi-driver/src/devices/Mlx90614/sensor.jpg

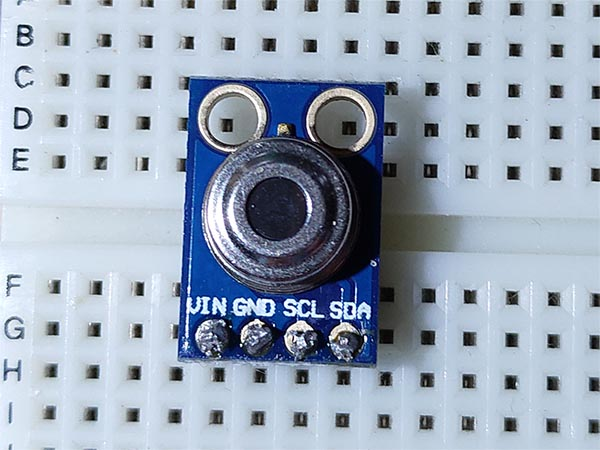
Programmer/iot-sunxi-driver/src/devices/Mlx90614/sensor.jpg
