LuCy4n3/SmartPotProject/Programmer/iot-sunxi-driver/src/devices/Mpr121/samples/ChannelStatuses.png

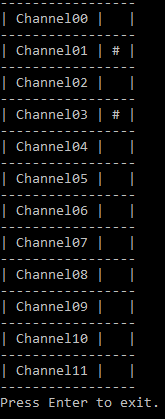
Programmer/iot-sunxi-driver/src/devices/Mpr121/samples/ChannelStatuses.png
