LuCy4n3/SmartPotProject/Programmer/iot-sunxi-driver/src/devices/Mpu9250/samples/Mpu9250_bb.png

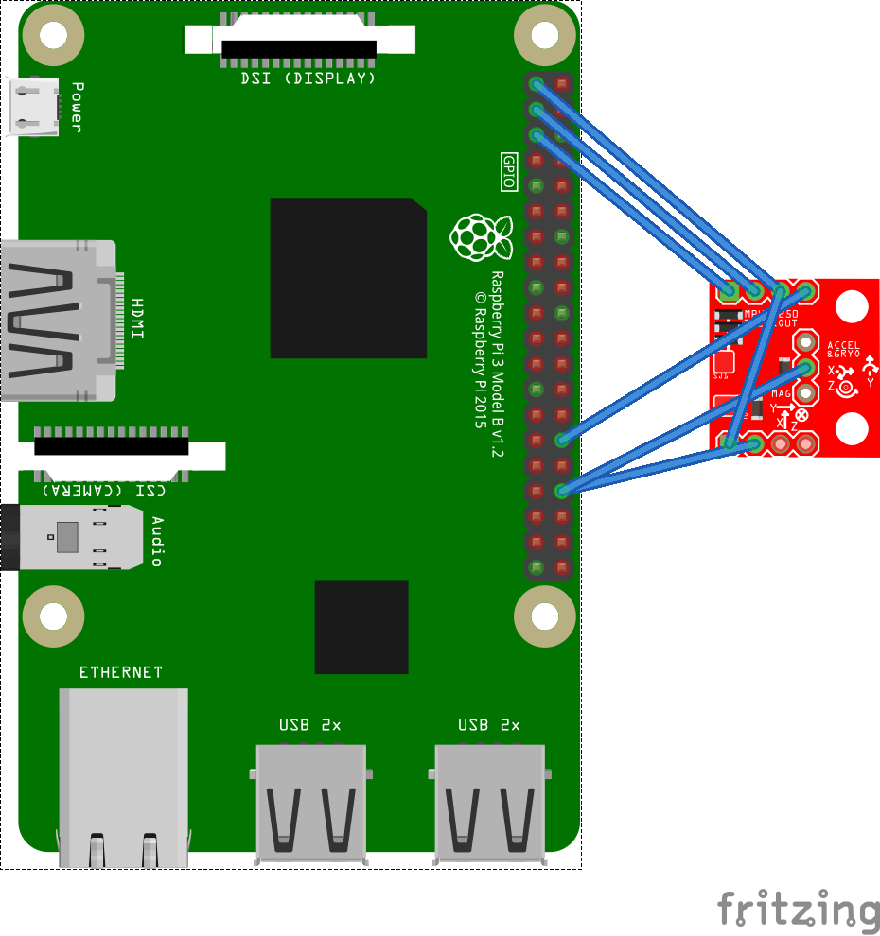
Programmer/iot-sunxi-driver/src/devices/Mpu9250/samples/Mpu9250_bb.png
