LuCy4n3/SmartPotProject/Programmer/iot-sunxi-driver/src/devices/Nrf24l01/samples/NRF_circuit_bb.jpg

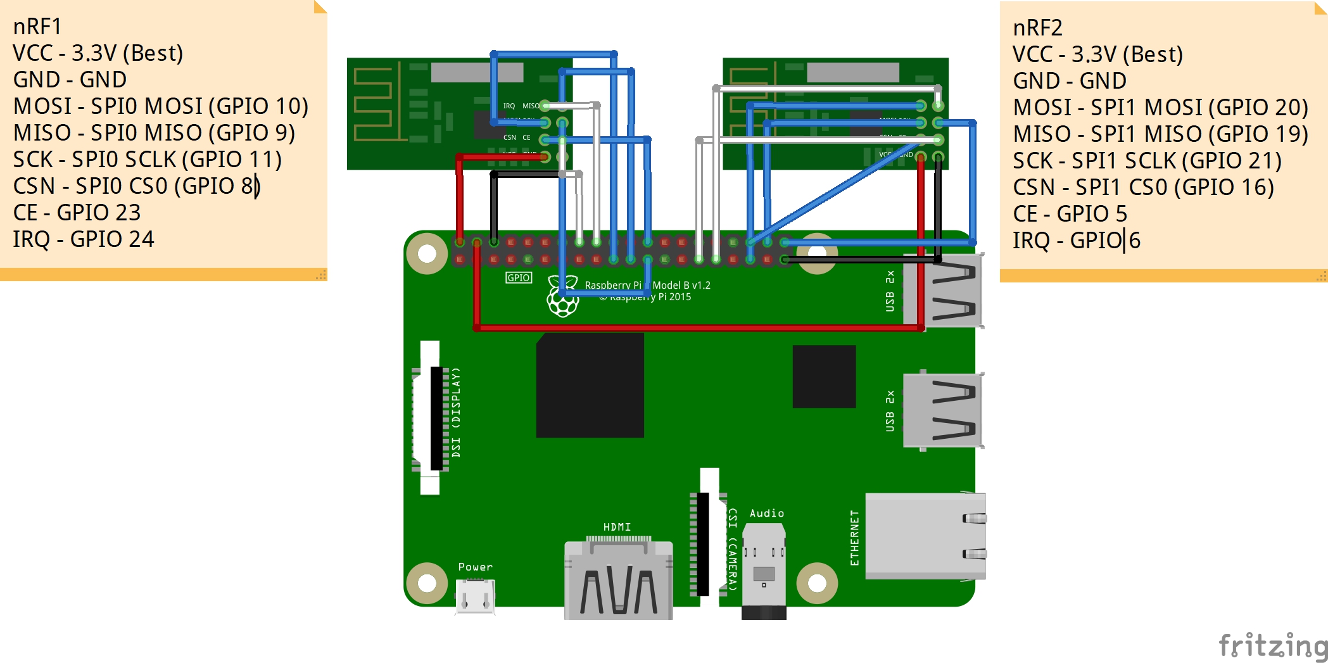
Programmer/iot-sunxi-driver/src/devices/Nrf24l01/samples/NRF_circuit_bb.jpg
