LuCy4n3/SmartPotProject/Programmer/iot-sunxi-driver/src/devices/Nrf24l01/sensor.jpg

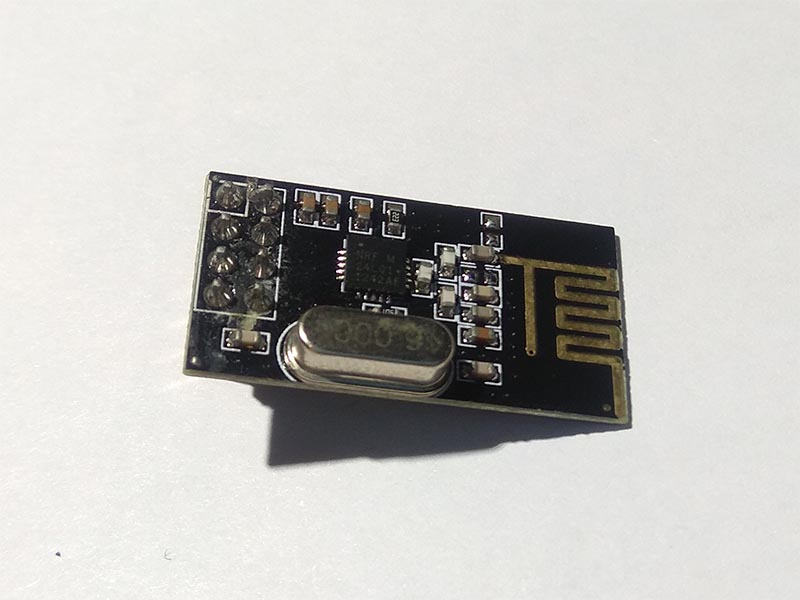
Programmer/iot-sunxi-driver/src/devices/Nrf24l01/sensor.jpg
