LuCy4n3/SmartPotProject/Programmer/iot-sunxi-driver/src/devices/Pca95x4/samples/Pca95x4_I2c_WriteLeds.png

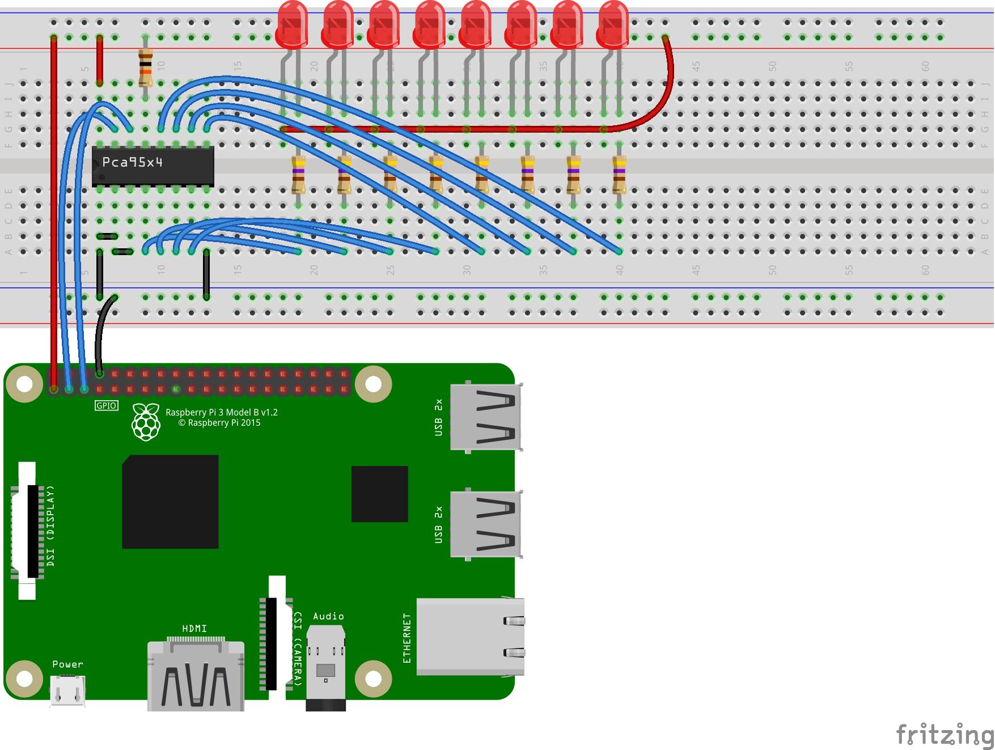
Programmer/iot-sunxi-driver/src/devices/Pca95x4/samples/Pca95x4_I2c_WriteLeds.png
