LuCy4n3/SmartPotProject/Programmer/iot-sunxi-driver/src/devices/RadioReceiver/Devices/Tea5767/sensor.jpg

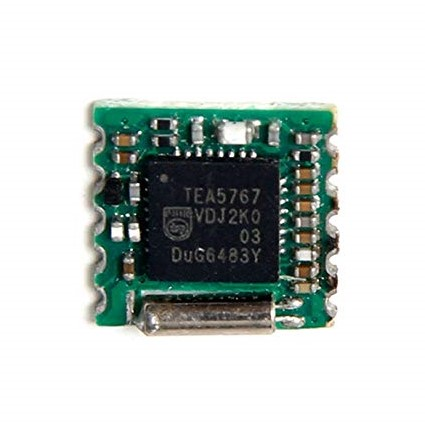
Programmer/iot-sunxi-driver/src/devices/RadioReceiver/Devices/Tea5767/sensor.jpg
