LuCy4n3/SmartPotProject/Programmer/iot-sunxi-driver/src/devices/RadioTransmitter/Devices/Kt0803/sensor.jpg

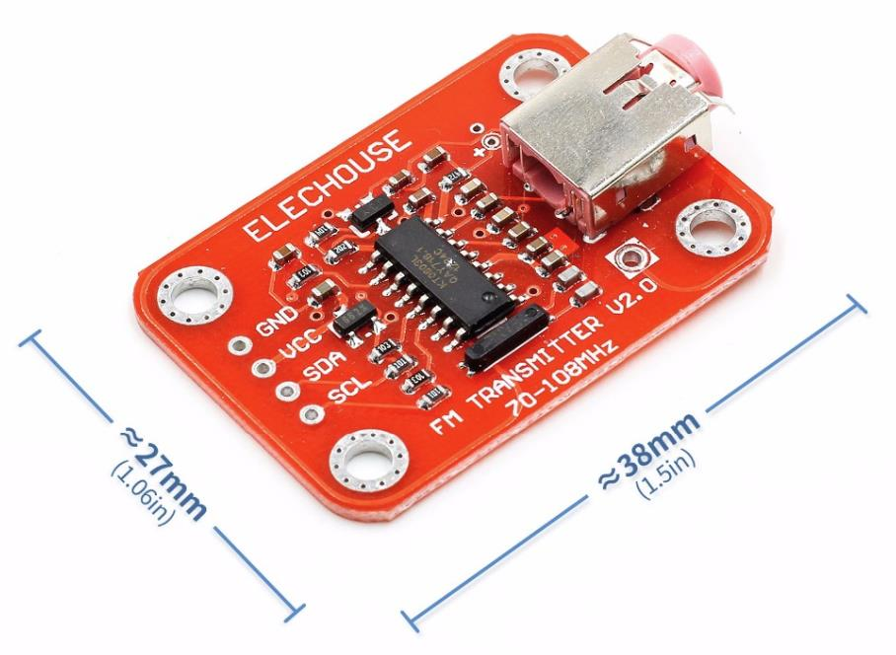
Programmer/iot-sunxi-driver/src/devices/RadioTransmitter/Devices/Kt0803/sensor.jpg
