LuCy4n3/SmartPotProject/Programmer/iot-sunxi-driver/src/devices/Rtc/Devices/Ds1307/sensor.jpg

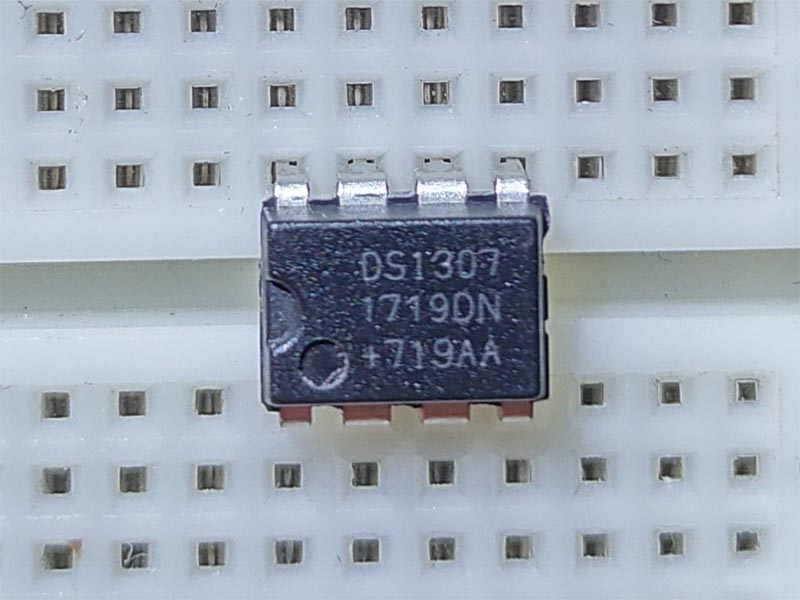
Programmer/iot-sunxi-driver/src/devices/Rtc/Devices/Ds1307/sensor.jpg
