LuCy4n3/SmartPotProject/Programmer/iot-sunxi-driver/src/devices/Rtc/Devices/Ds3231/sensor.jpg

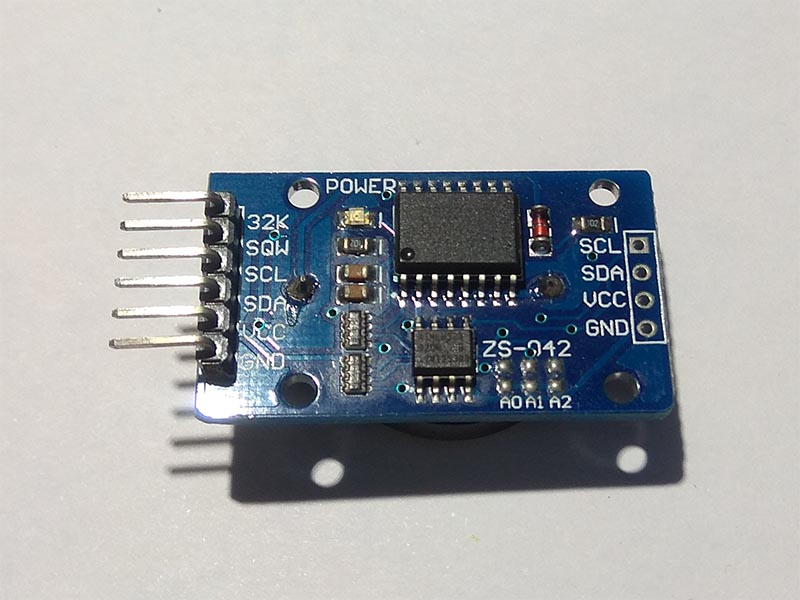
Programmer/iot-sunxi-driver/src/devices/Rtc/Devices/Ds3231/sensor.jpg
