LuCy4n3/SmartPotProject/Programmer/iot-sunxi-driver/src/devices/Rtc/Devices/Pcf8563/sensor.jpg

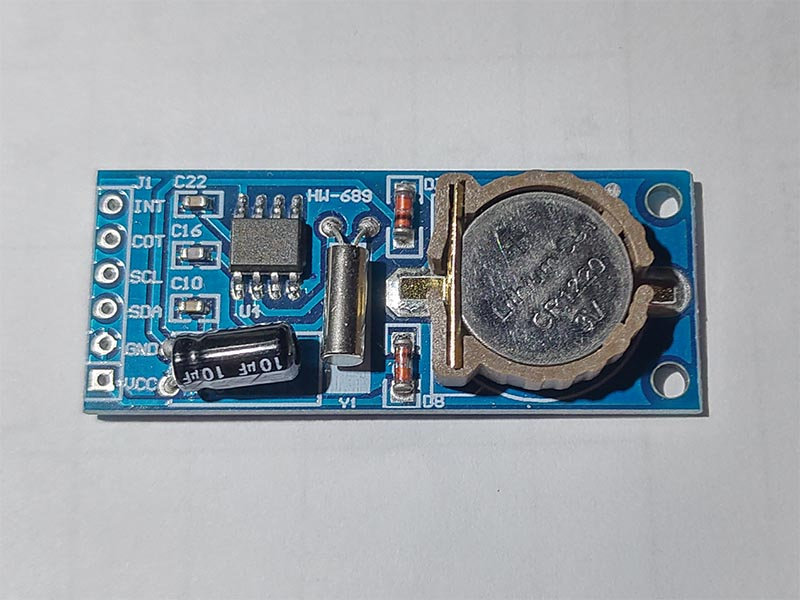
Programmer/iot-sunxi-driver/src/devices/Rtc/Devices/Pcf8563/sensor.jpg
