LuCy4n3/SmartPotProject/Programmer/iot-sunxi-driver/src/devices/Rtc/samples/Circuit_DS1307_bb.png

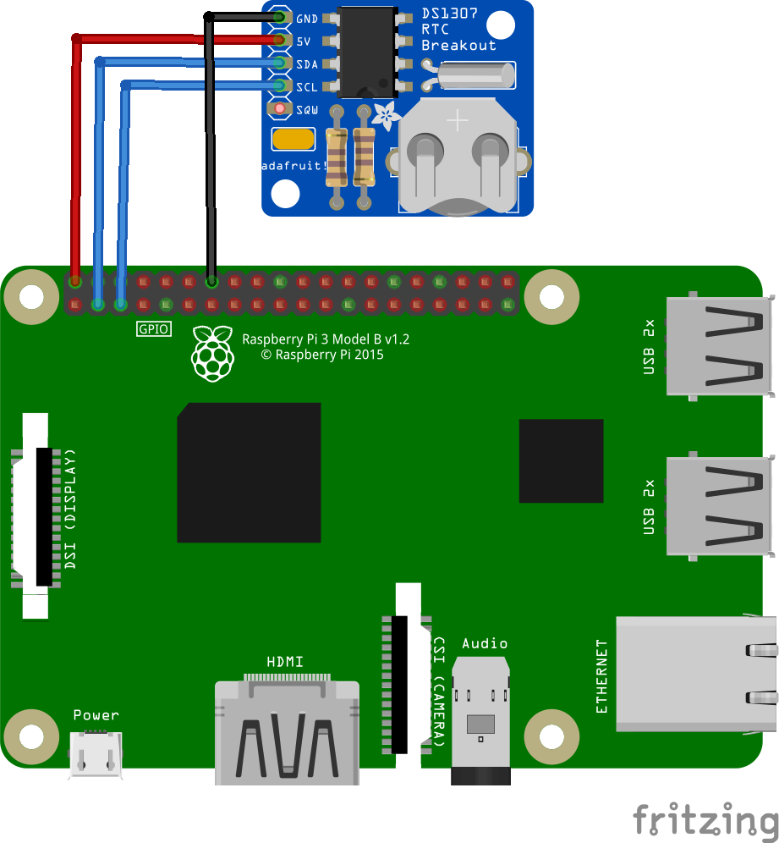
Programmer/iot-sunxi-driver/src/devices/Rtc/samples/Circuit_DS1307_bb.png
