LuCy4n3/SmartPotProject/Programmer/iot-sunxi-driver/src/devices/Seesaw/samples/SeesawSampleBlinkingLights_bb.png

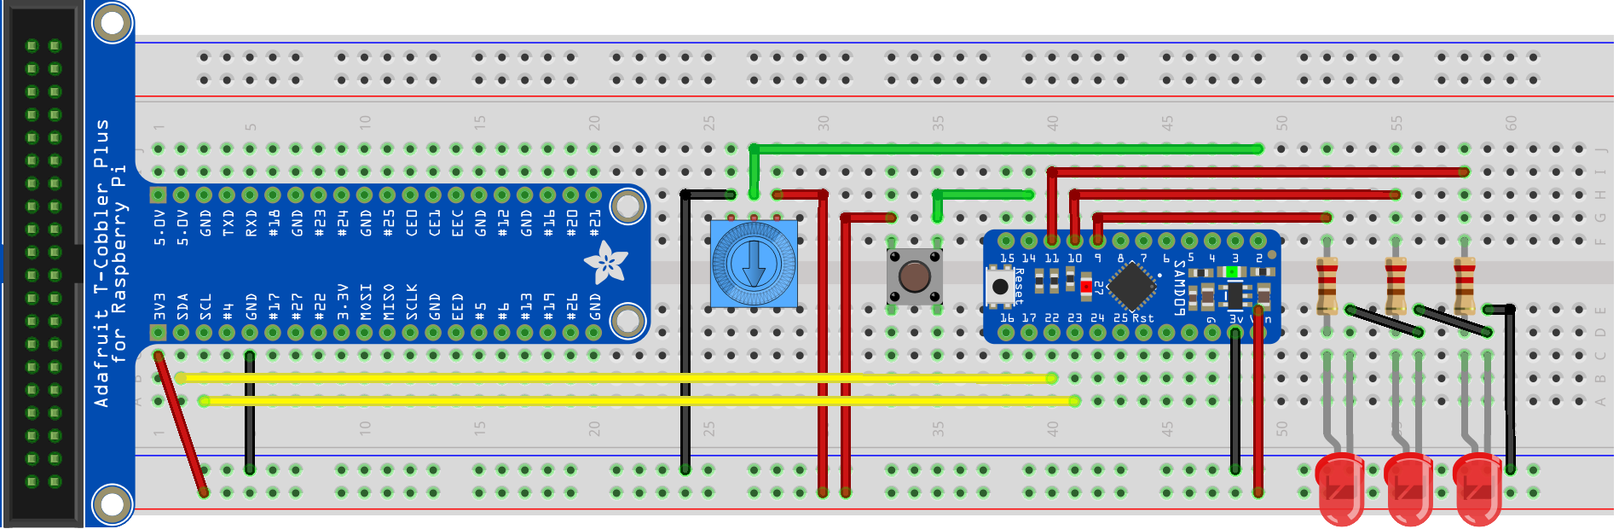
Programmer/iot-sunxi-driver/src/devices/Seesaw/samples/SeesawSampleBlinkingLights_bb.png
