LuCy4n3/SmartPotProject/Programmer/iot-sunxi-driver/src/devices/Seesaw/samples/SeesawSampleCapabilities_bb.png

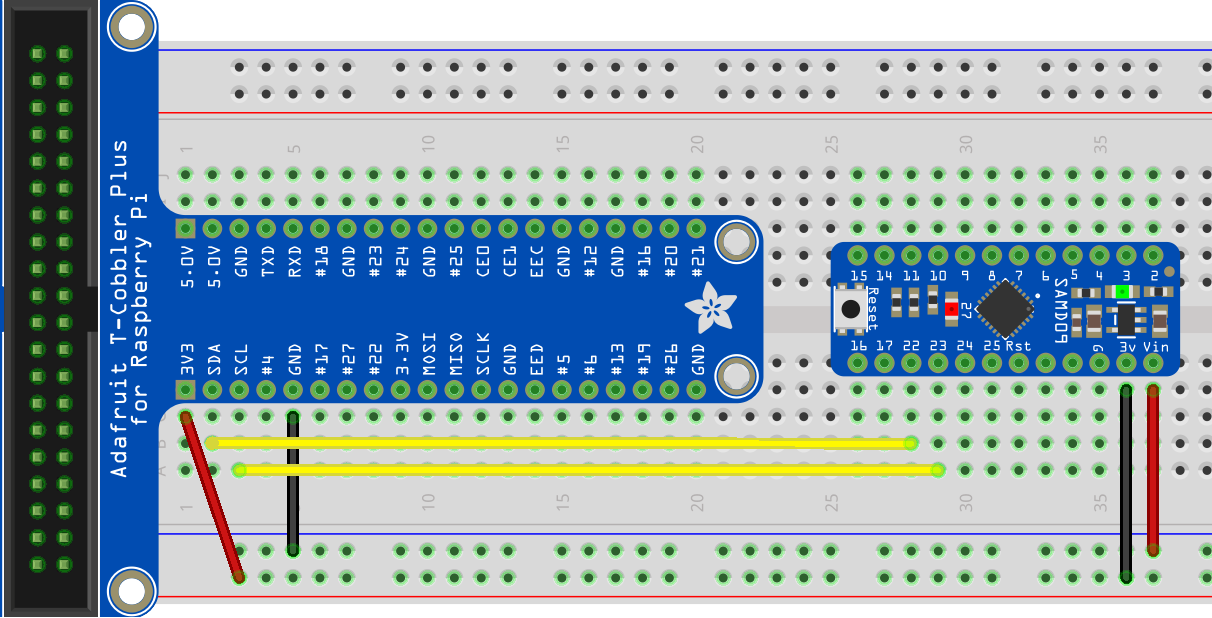
Programmer/iot-sunxi-driver/src/devices/Seesaw/samples/SeesawSampleCapabilities_bb.png
