LuCy4n3/SmartPotProject/Programmer/iot-sunxi-driver/src/devices/ServoMotor/samples/ServoMotor.png

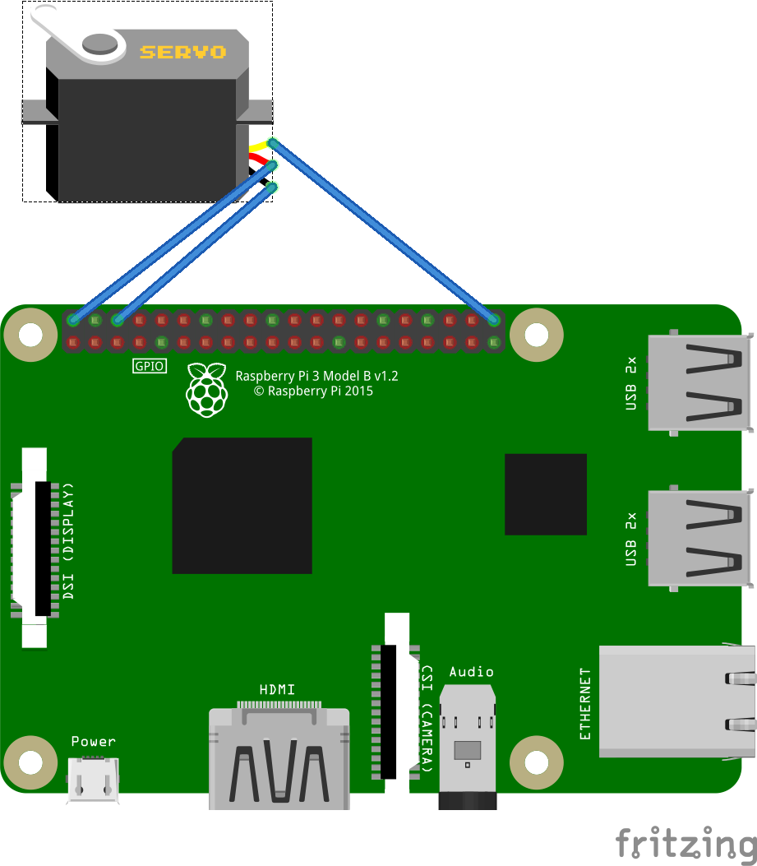
Programmer/iot-sunxi-driver/src/devices/ServoMotor/samples/ServoMotor.png
