LuCy4n3/SmartPotProject/Programmer/iot-sunxi-driver/src/devices/Sht3x/sensor.jpg

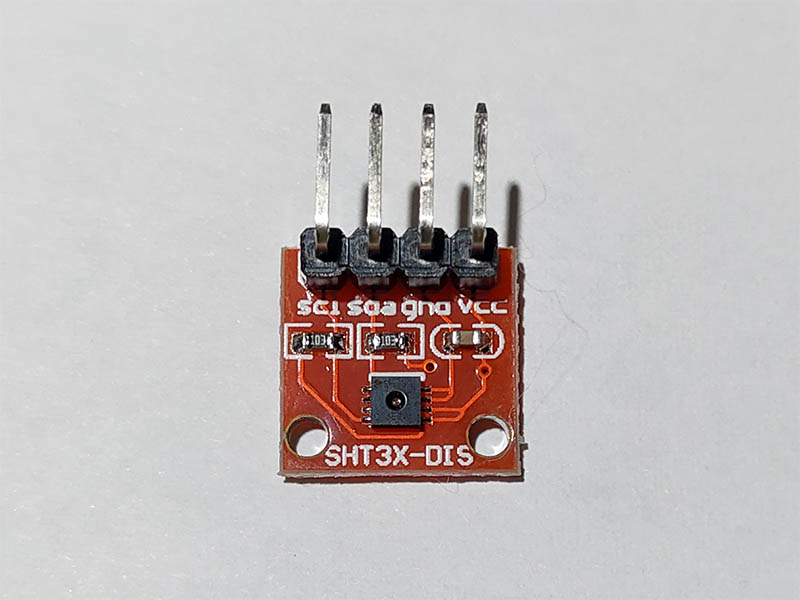
Programmer/iot-sunxi-driver/src/devices/Sht3x/sensor.jpg
