LuCy4n3/SmartPotProject/Programmer/iot-sunxi-driver/src/devices/Si7021/samples/Si7021_I2c_Read_Temp_Humidity.png

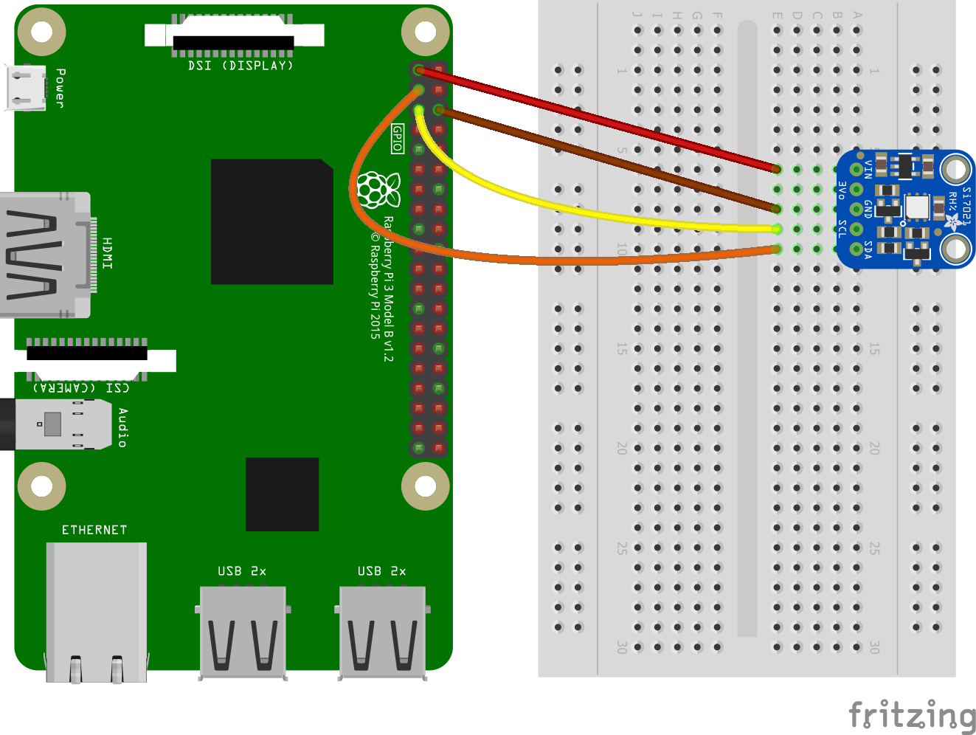
Programmer/iot-sunxi-driver/src/devices/Si7021/samples/Si7021_I2c_Read_Temp_Humidity.png
