LuCy4n3/SmartPotProject/Programmer/iot-sunxi-driver/src/devices/Si7021/sensor.jpg

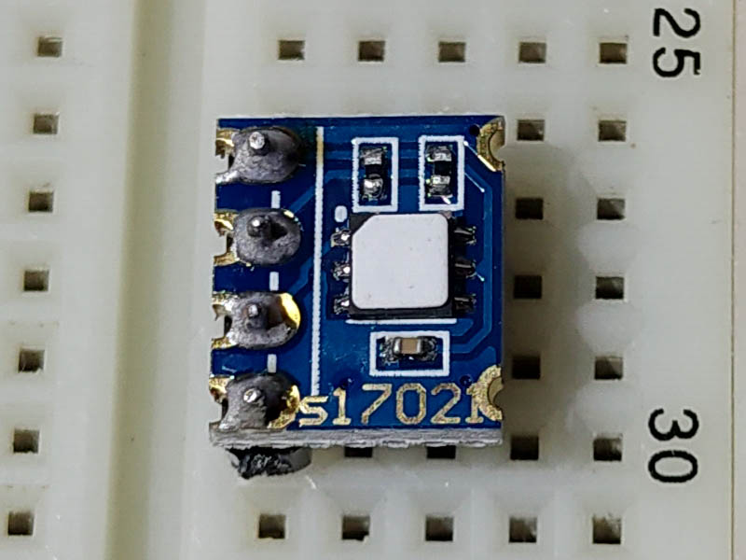
Programmer/iot-sunxi-driver/src/devices/Si7021/sensor.jpg
