LuCy4n3/SmartPotProject/Programmer/iot-sunxi-driver/src/devices/SoftPwm/samples/pwmled.png

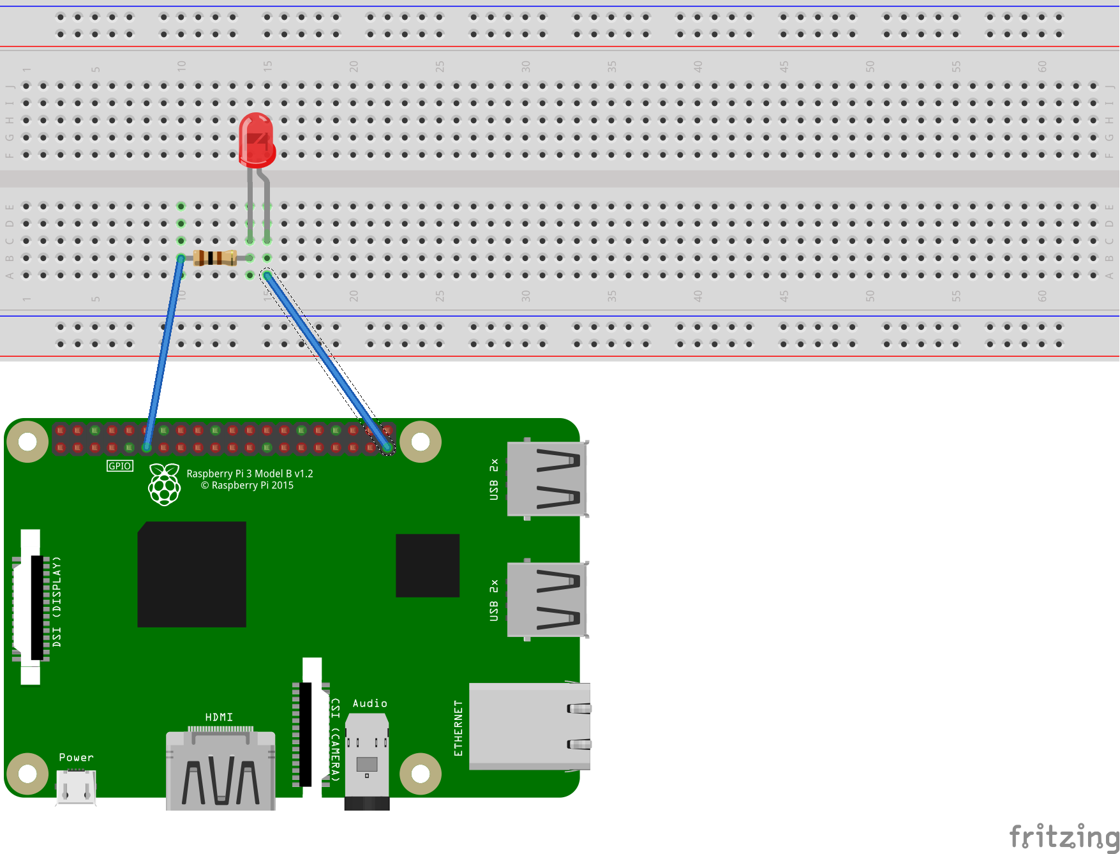
Programmer/iot-sunxi-driver/src/devices/SoftPwm/samples/pwmled.png
