LuCy4n3/SmartPotProject/Programmer/iot-sunxi-driver/src/devices/Ssd13xx/samples/Ssd1306_I2c_PiOled.png

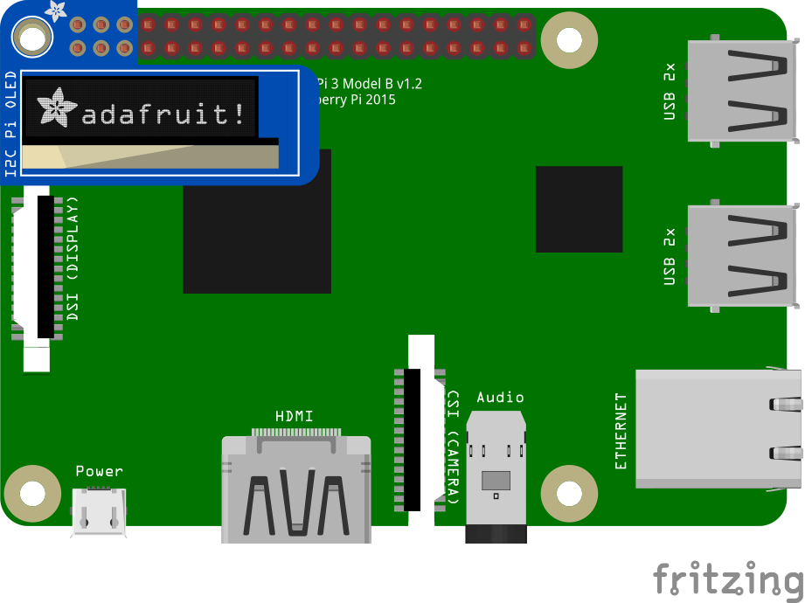
Programmer/iot-sunxi-driver/src/devices/Ssd13xx/samples/Ssd1306_I2c_PiOled.png
