LuCy4n3/SmartPotProject/Programmer/iot-sunxi-driver/src/devices/Ssd1351/samples/images/breakoutboard.png

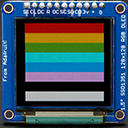
Programmer/iot-sunxi-driver/src/devices/Ssd1351/samples/images/breakoutboard.png
