LuCy4n3/SmartPotProject/Programmer/iot-sunxi-driver/src/devices/Ssd1351/samples/Ssd1351.Sample.png

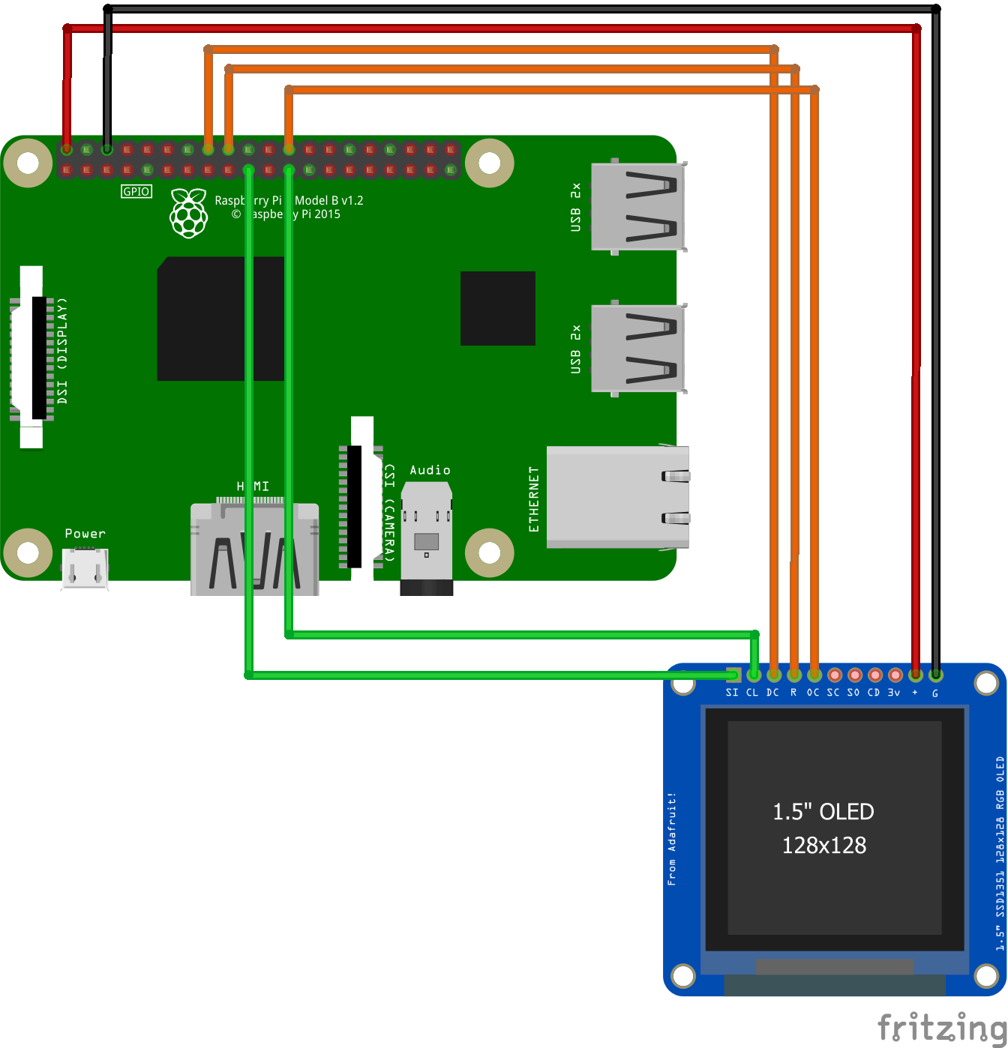
Programmer/iot-sunxi-driver/src/devices/Ssd1351/samples/Ssd1351.Sample.png
