LuCy4n3/SmartPotProject/Programmer/iot-sunxi-driver/src/devices/Tm1637/samples/tm1637_bb.png

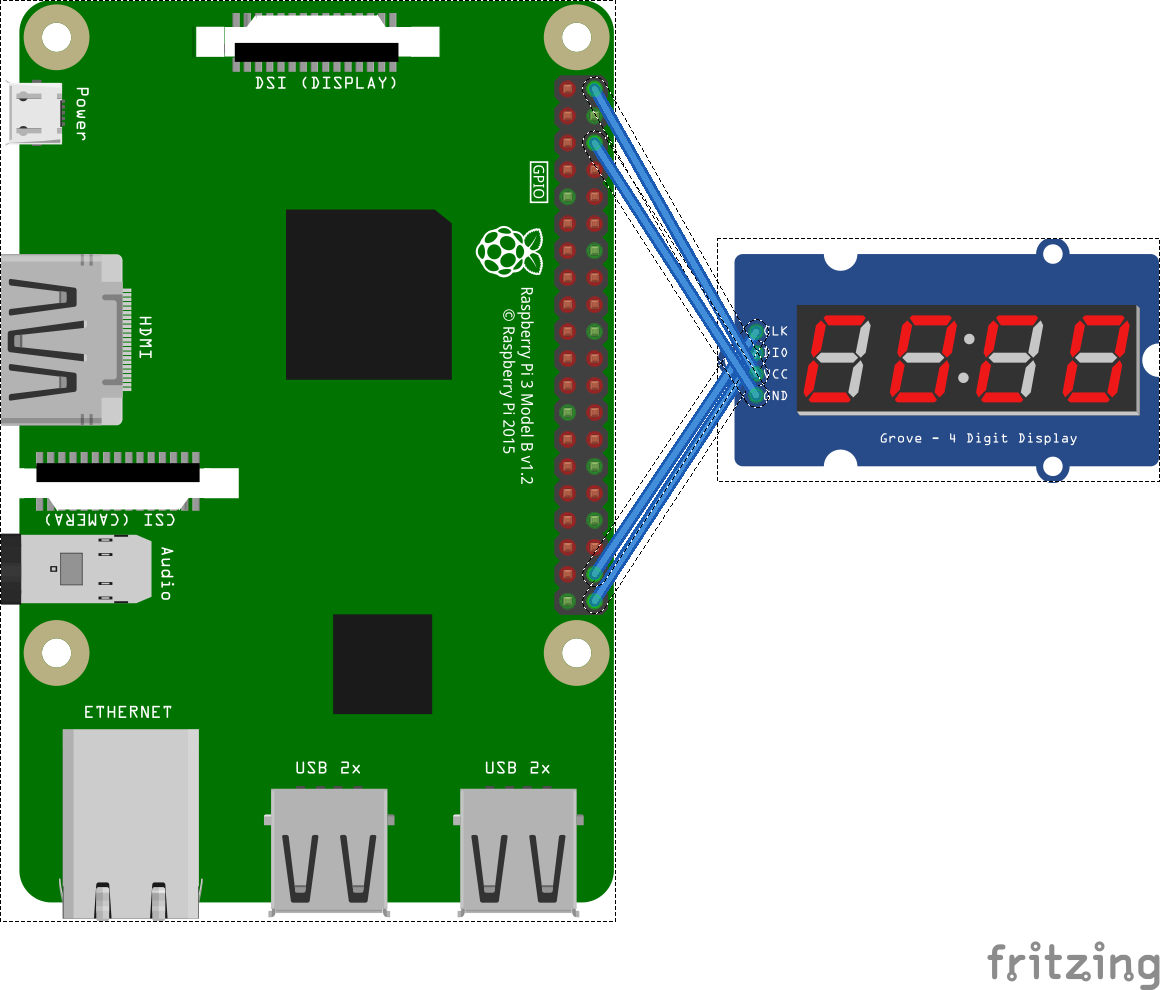
Programmer/iot-sunxi-driver/src/devices/Tm1637/samples/tm1637_bb.png
