LuCy4n3/SmartPotProject/Programmer/iot-sunxi-driver/src/devices/Uln2003/samples/Uln2003.png

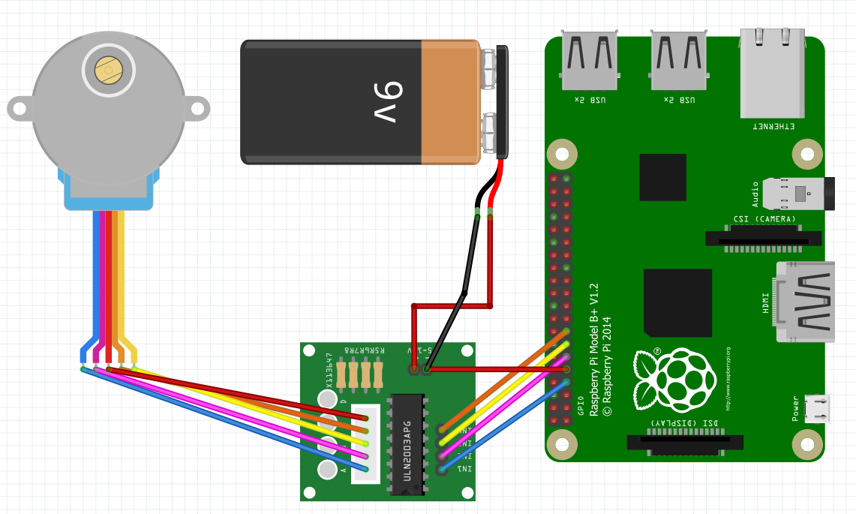
Programmer/iot-sunxi-driver/src/devices/Uln2003/samples/Uln2003.png
