LuCy4n3/SmartPotProject/Programmer/iot-sunxi-driver/src/devices/Vl53L0X/VL53L0X.jpg

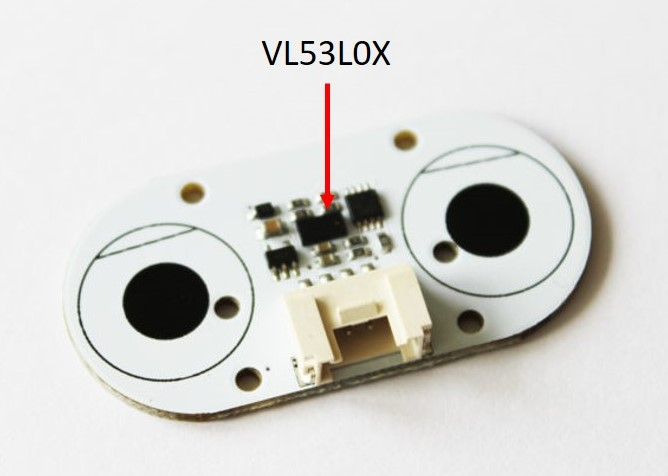
Programmer/iot-sunxi-driver/src/devices/Vl53L0X/VL53L0X.jpg
