LuCy4n3/SmartPotProject/Programmer/iot-sunxi-driver/src/devices/Ws28xx/samples/rpi-neo-pixels_bb.png

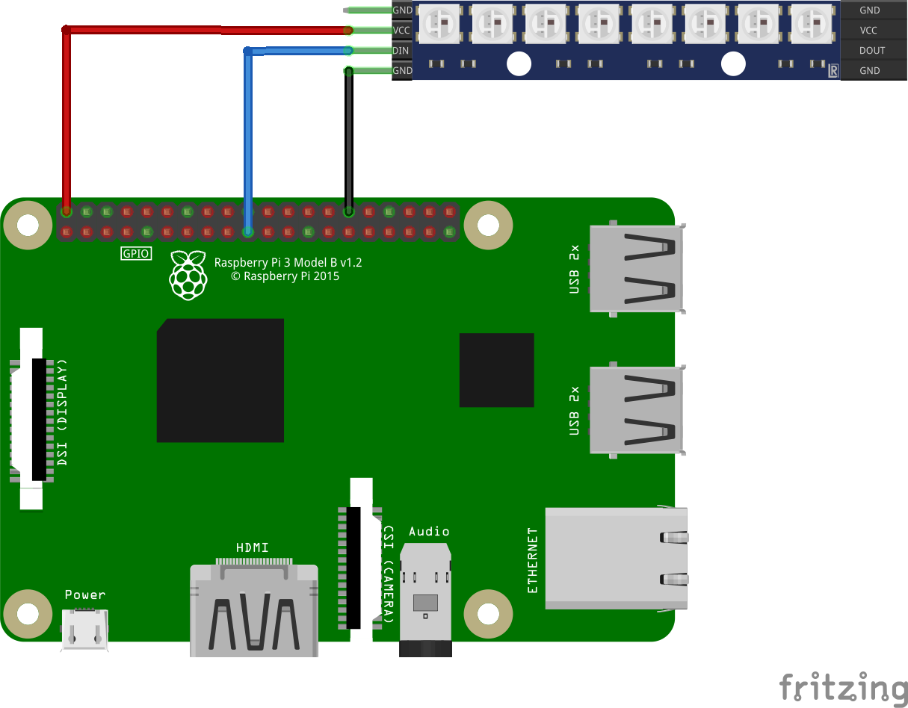
Programmer/iot-sunxi-driver/src/devices/Ws28xx/samples/rpi-neo-pixels_bb.png
