LuCy4n3/SmartPotProject/Programmer/iot-sunxi-driver/src/devices/Ws28xx/samples/WS2808.png

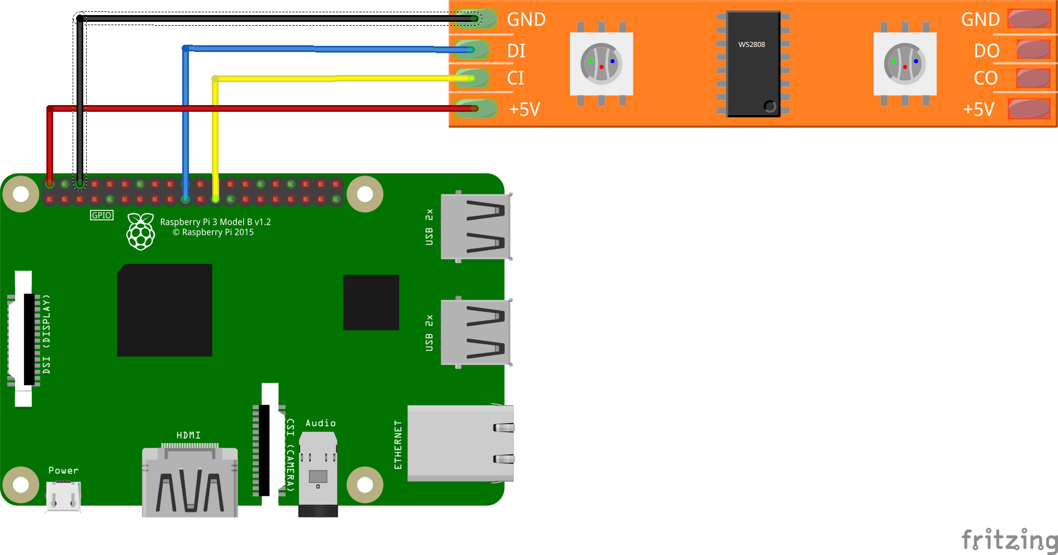
Programmer/iot-sunxi-driver/src/devices/Ws28xx/samples/WS2808.png
