LuCy4n3/SmartPotProject/Programmer/ITDaysDemo/Resources/Bottom - lumina normala.png

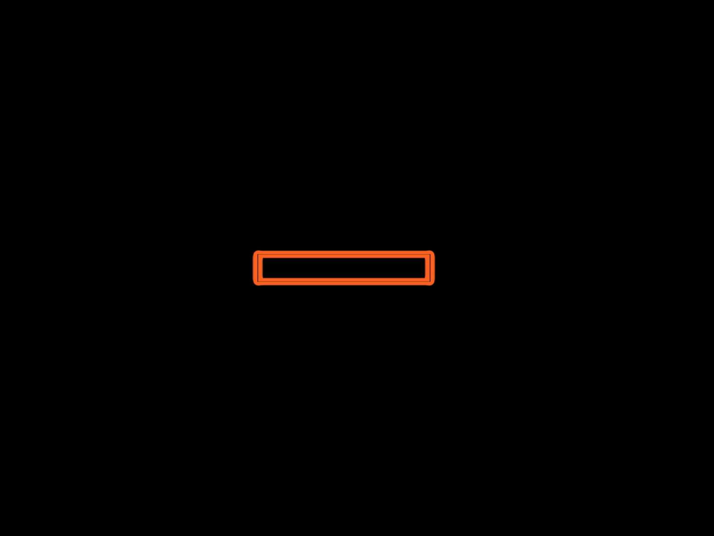
Programmer/ITDaysDemo/Resources/Bottom - lumina normala.png
