LuCy4n3/SmartPotProject/Programmer/ITDaysDemo/Resources/Centered __dimming.png

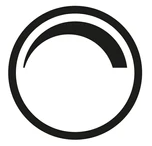
Programmer/ITDaysDemo/Resources/Centered __dimming.png
