LuCy4n3/SmartPotProject/SQLserverFinale/SQLserverFinale/wwwroot/images/arhiva of.png

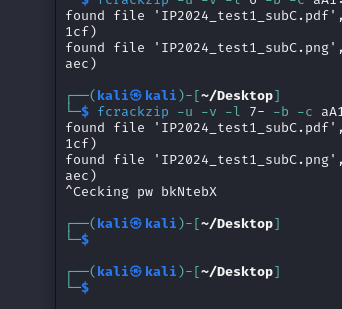
SQLserverFinale/SQLserverFinale/wwwroot/images/arhiva of.png
