LuCy4n3/SmartPotProject/Programmer/iot-sunxi-driver/samples/serialport-arduino/setup-close.jpg

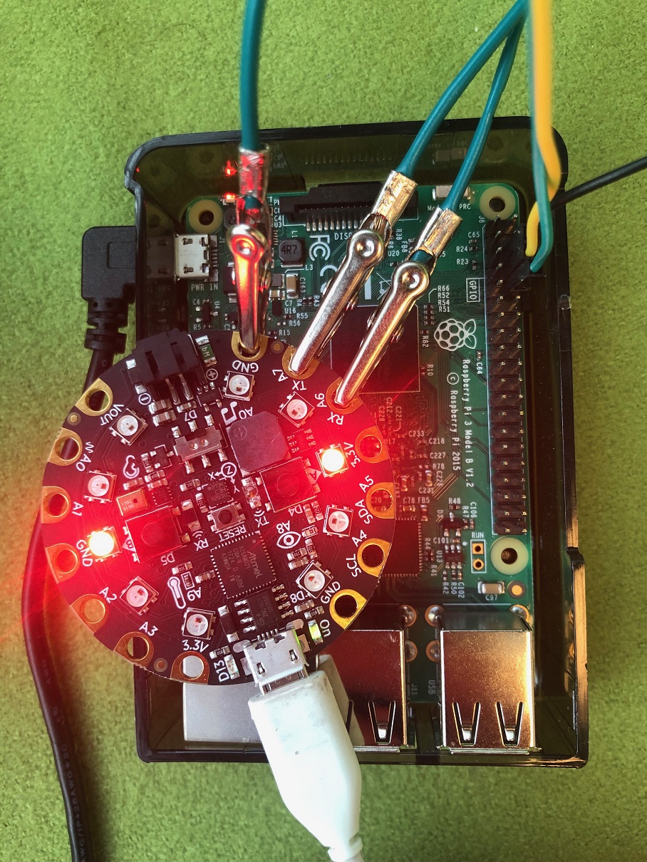
Programmer/iot-sunxi-driver/samples/serialport-arduino/setup-close.jpg
