LuCy4n3/SmartPotProject/Programmer/iot-sunxi-driver/samples/serialport-arduino/setup-full.jpg

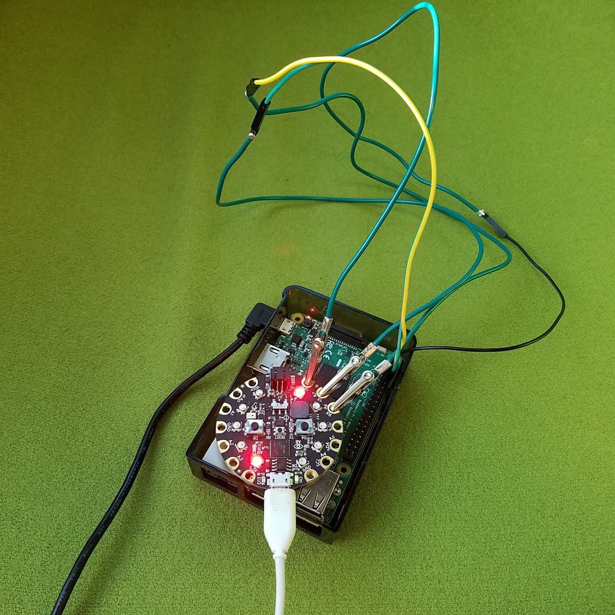
Programmer/iot-sunxi-driver/samples/serialport-arduino/setup-full.jpg
