LuCy4n3/SmartPotProject/Programmer/iot-sunxi-driver/src/devices/Buzzer/samples/Buzzer.Samples.wiring.png

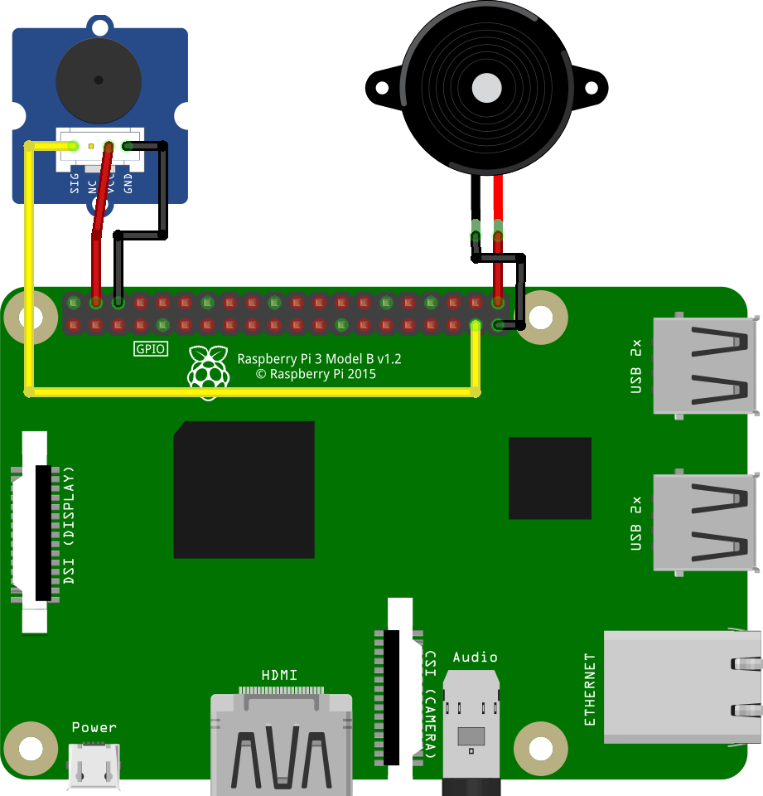
Programmer/iot-sunxi-driver/src/devices/Buzzer/samples/Buzzer.Samples.wiring.png
