LuCy4n3/SmartPotProject/Programmer/iot-sunxi-driver/src/devices/CharacterLcd/samples/lcmWiringExample.jpg

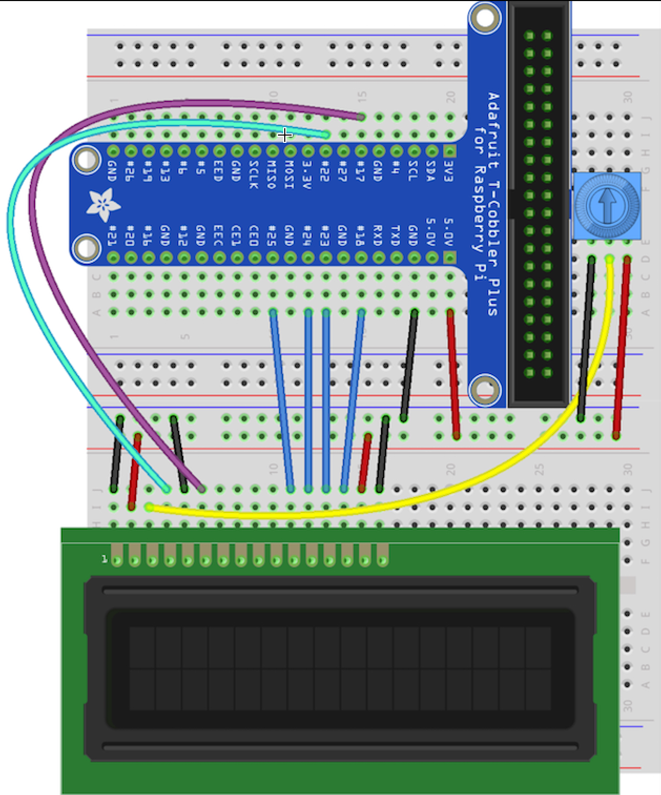
Programmer/iot-sunxi-driver/src/devices/CharacterLcd/samples/lcmWiringExample.jpg
