LuCy4n3/SmartPotProject/CameraCode/test.jpg

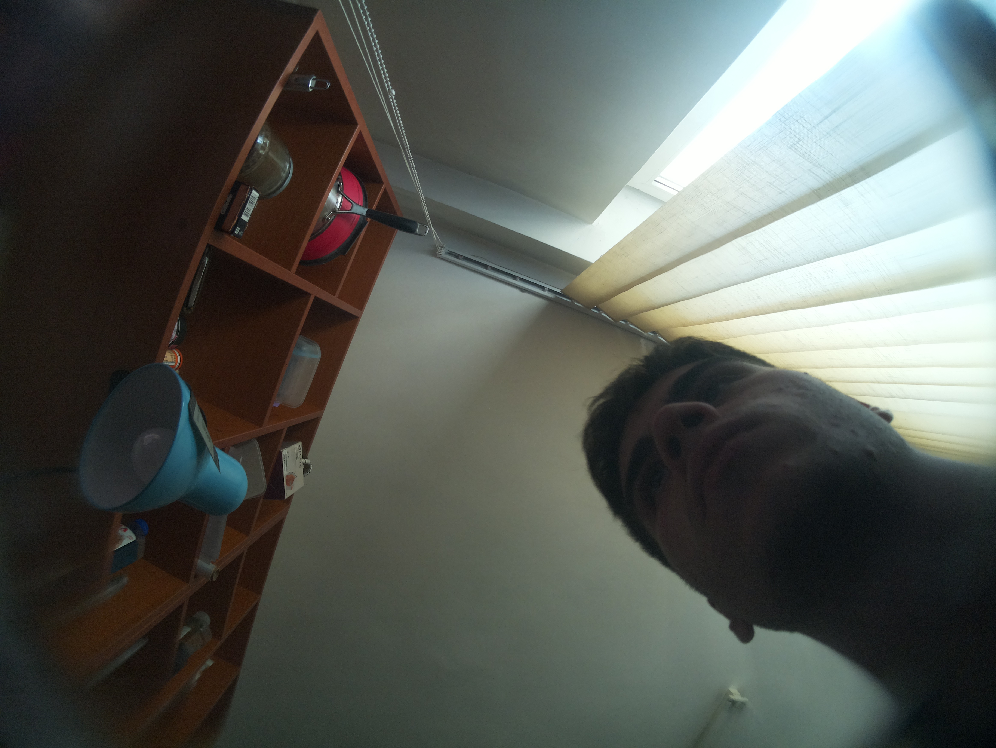
CameraCode/test.jpg
