LuCy4n3/SmartPotProject/Programmer/iot-sunxi-driver/src/devices/Ads1115/samples/RunningResult.jpg

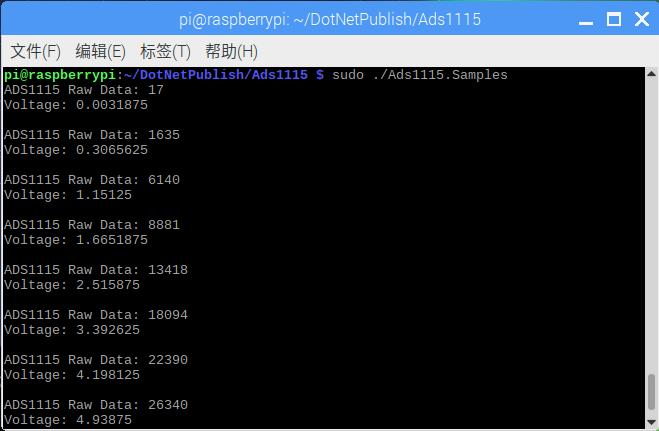
Programmer/iot-sunxi-driver/src/devices/Ads1115/samples/RunningResult.jpg
