LuCy4n3/SmartPotProject/Programmer/iot-sunxi-driver/src/devices/Adxl345/samples/RunningResult.jpg

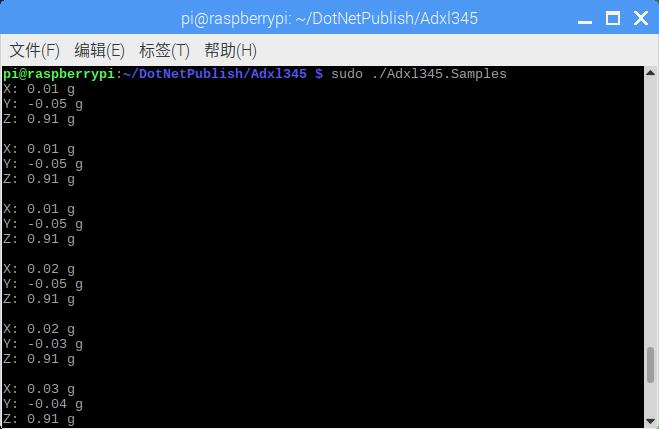
Programmer/iot-sunxi-driver/src/devices/Adxl345/samples/RunningResult.jpg
