LuCy4n3/SmartPotProject/Programmer/iot-sunxi-driver/src/devices/Hcsr501/samples/RunningResult.gif

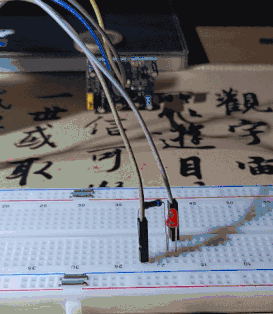
Programmer/iot-sunxi-driver/src/devices/Hcsr501/samples/RunningResult.gif
