LuCy4n3/SmartPotProject/Programmer/iot-sunxi-driver/src/devices/Mlx90614/samples/RunningResult.jpg

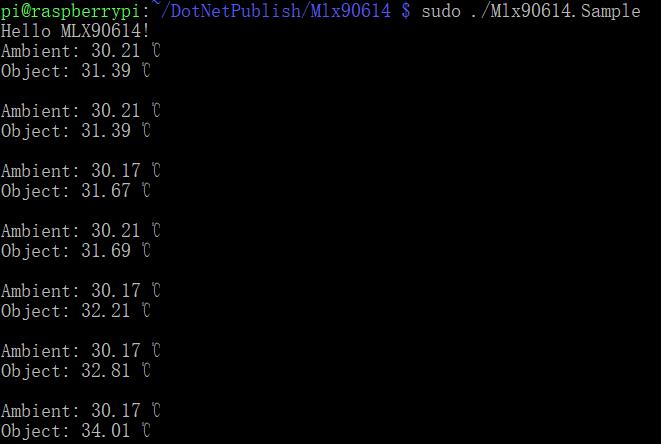
Programmer/iot-sunxi-driver/src/devices/Mlx90614/samples/RunningResult.jpg
