LuCy4n3/SmartPotProject/Programmer/iot-sunxi-driver/src/devices/Nrf24l01/samples/RunningResult.jpg

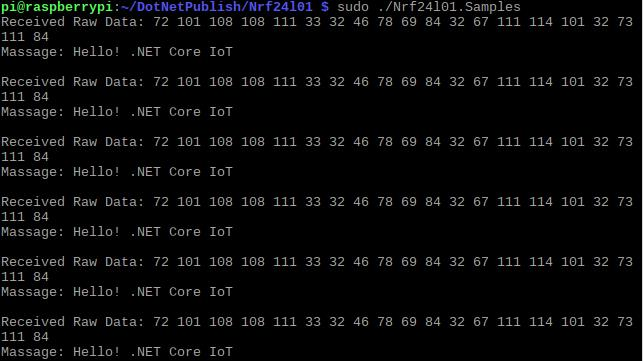
Programmer/iot-sunxi-driver/src/devices/Nrf24l01/samples/RunningResult.jpg
