LuCy4n3/SmartPotProject/Programmer/iot-sunxi-driver/src/devices/Rtc/samples/RunningResult.jpg

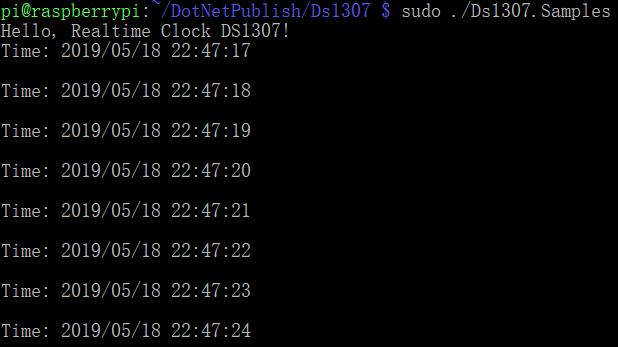
Programmer/iot-sunxi-driver/src/devices/Rtc/samples/RunningResult.jpg
