LuCy4n3/SmartPotProject/proj_test/importantDocumentation/LifeCycles.png

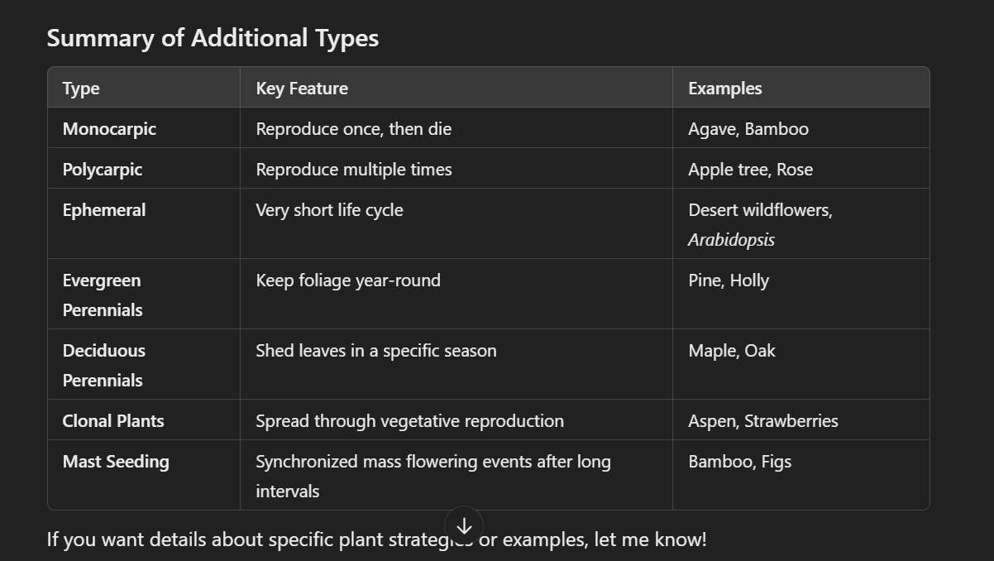
proj_test/importantDocumentation/LifeCycles.png
