LuCy4n3/SmartPotProject/proj_test/importantDocumentation/LifeCyclesSimple.png

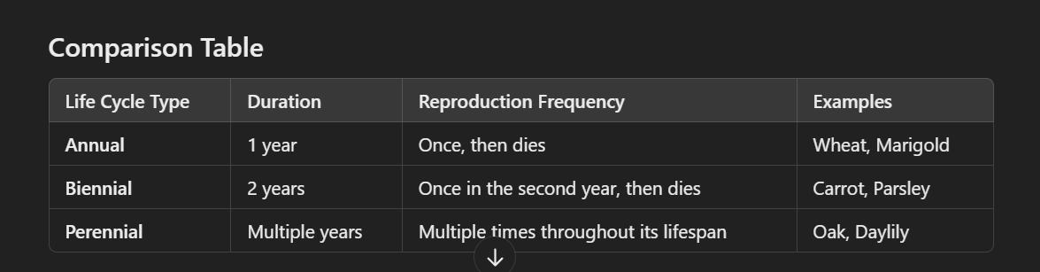
proj_test/importantDocumentation/LifeCyclesSimple.png
